IgnacioPardo/e36-obd/hardware/elm-backpack/viewer.html

E36 / HARDWARE · REV E

# Inline ECU adapter

48 mm narrow body · Hidden mounting · Rear USB

FIT CHECK REQUIRED

WebGL is unavailable. Open assembled.png or exploded.png in the exports folder.

Drag to orbit · Scroll to zoom · Double-click to reset

## Assembly

ClosedOpenExploded

Silver highlights · optional paint

## Separation

Printed base Boards and connectors ELM reference housing

Enclosure

162 × 48 × 30.4

Printed parts

6

Wall / floor

2.4 / 2.4*

USB opening

32 wide

Wire entry

16 × 12

*Floor is 1.4 mm beneath recessed mounting straps. The longer tail has a separate support-tie position.

The ELM housing and electronics are provisional packaging references. Verify the real boards, solder and wire heights, contact areas and tail hole before printing the full enclosure.

## Files

Print layout · 3MFFirst print · fit gauge STLEditable assembly · STEPMeasurement sources and design planPrinting and assembly instructions
