IgnacioPardo/e36-obd/hardware/elm-backpack/exports/black.png

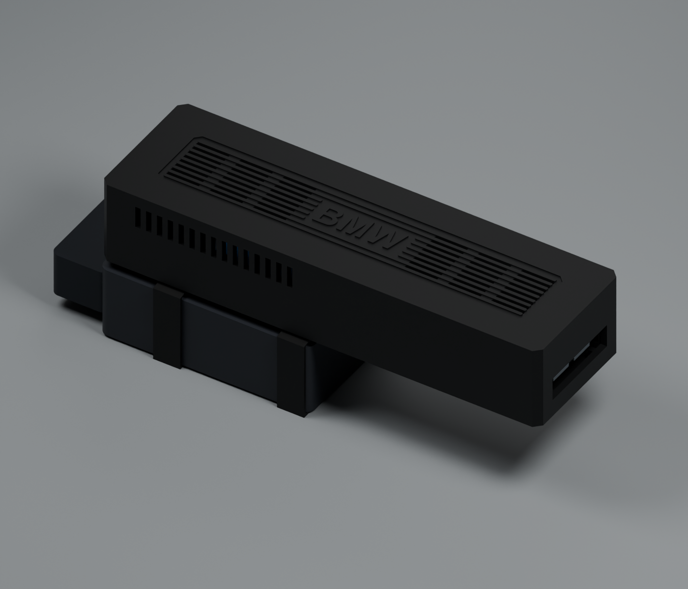
hardware/elm-backpack/exports/black.png
