IgnacioPardo/e36-obd/hardware/elm-backpack/exports/comparison.png

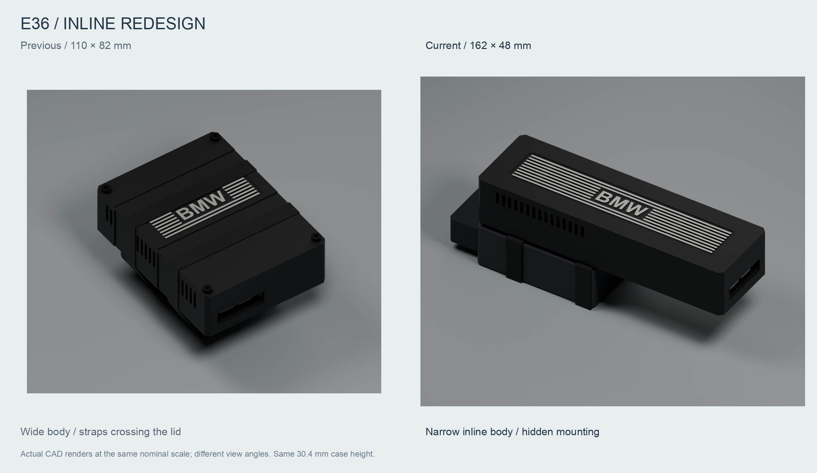
hardware/elm-backpack/exports/comparison.png
