IgnacioPardo/e36-obd/hardware/elm-backpack/exports/exploded-views/mounts-raw.png

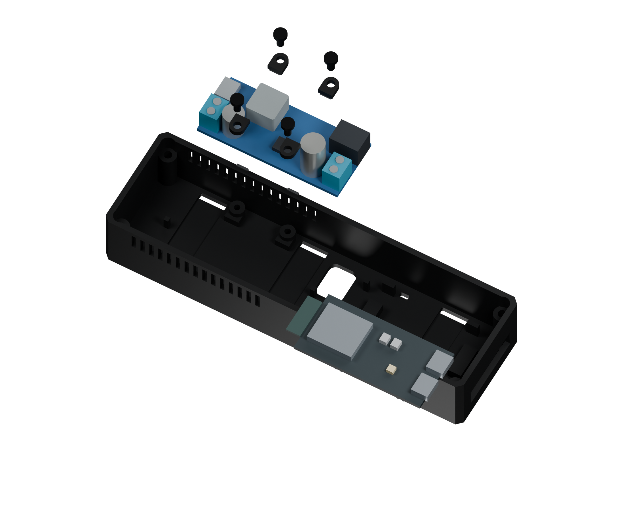
hardware/elm-backpack/exports/exploded-views/mounts-raw.png
