IgnacioPardo/e36-obd/hardware/elm-backpack/exports/exploded-views/mounts.png

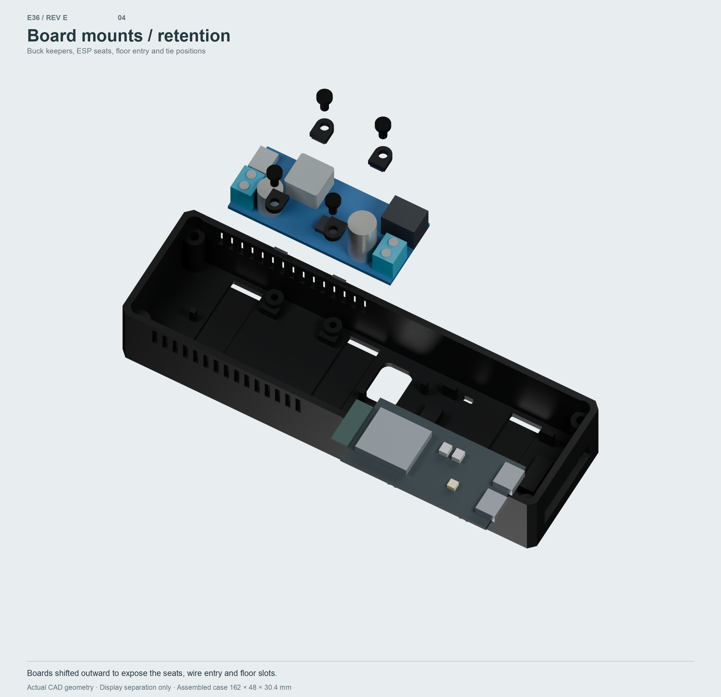
hardware/elm-backpack/exports/exploded-views/mounts.png
