IgnacioPardo/e36-obd/hardware/elm-backpack/exports/exploded-views/reverse-raw.png

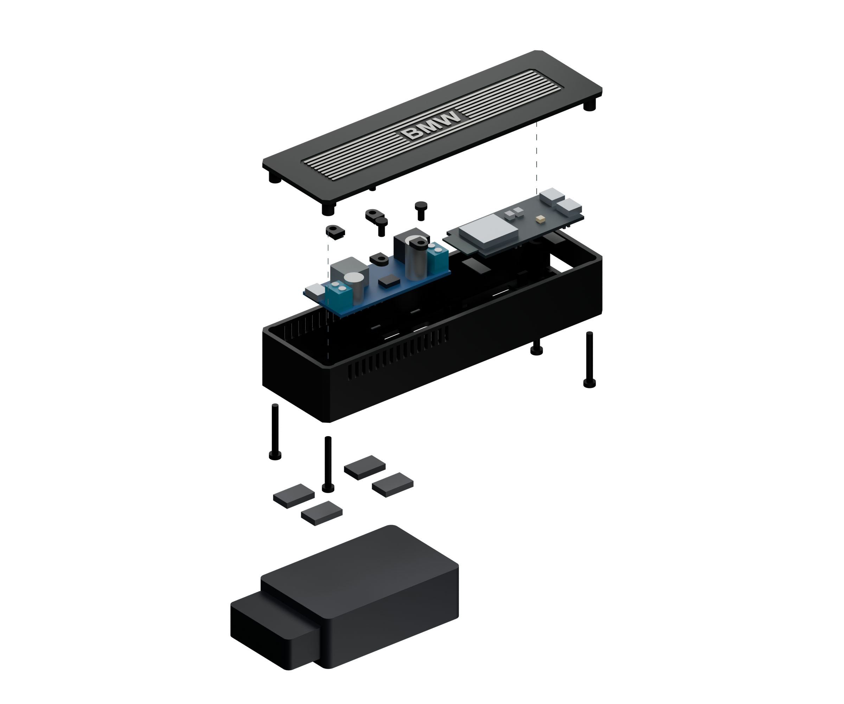
hardware/elm-backpack/exports/exploded-views/reverse-raw.png
