IgnacioPardo/e36-obd/hardware/elm-backpack/exports/exploded-views/reverse.png

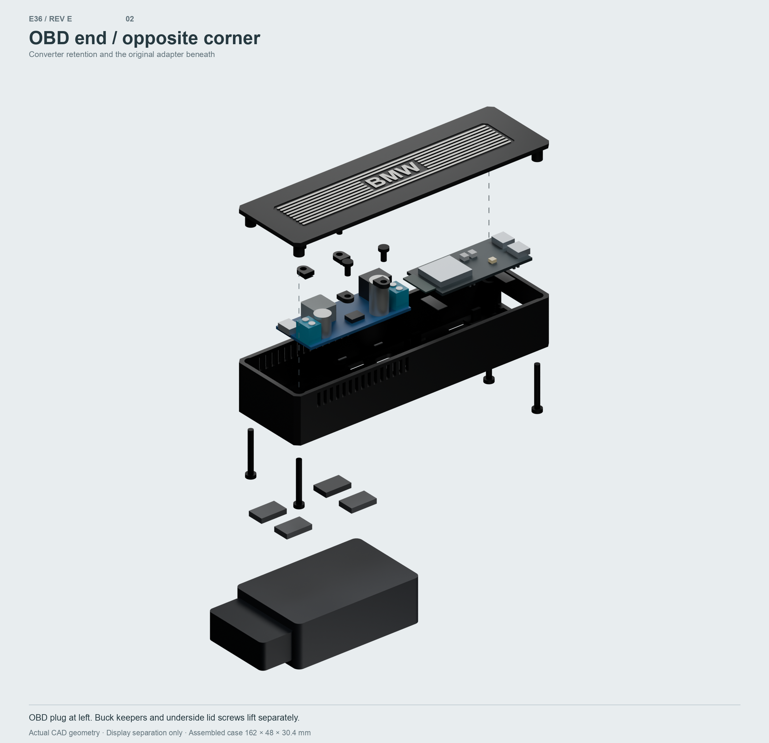
hardware/elm-backpack/exports/exploded-views/reverse.png
