IgnacioPardo/e36-obd/hardware/elm-backpack/exports/exploded-views/underside-raw.png

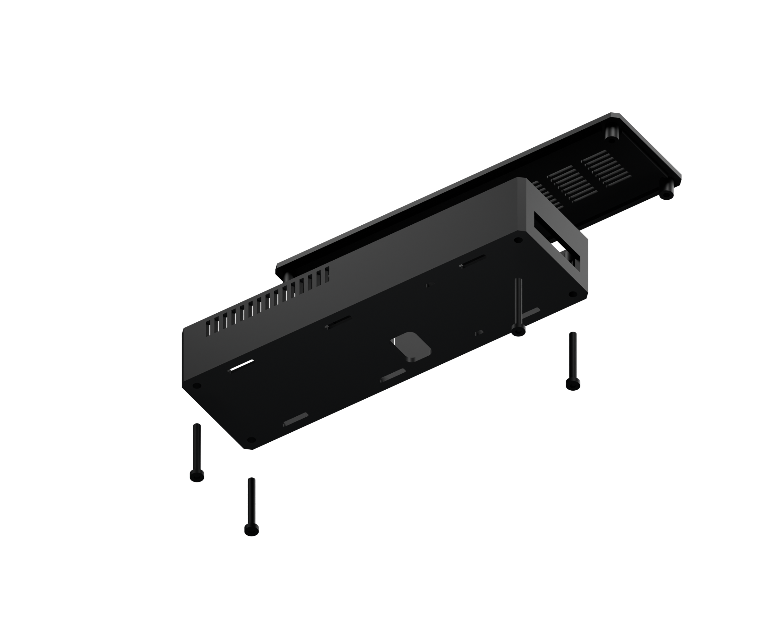
hardware/elm-backpack/exports/exploded-views/underside-raw.png
