IgnacioPardo/e36-obd/hardware/elm-backpack/exports/exploded-views/underside.png

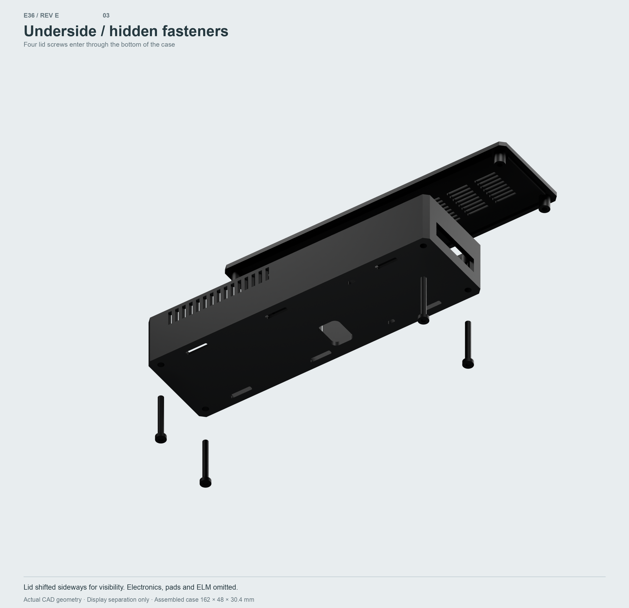
hardware/elm-backpack/exports/exploded-views/underside.png
