IgnacioPardo/e36-obd/hardware/elm-backpack/exports/exploded.png

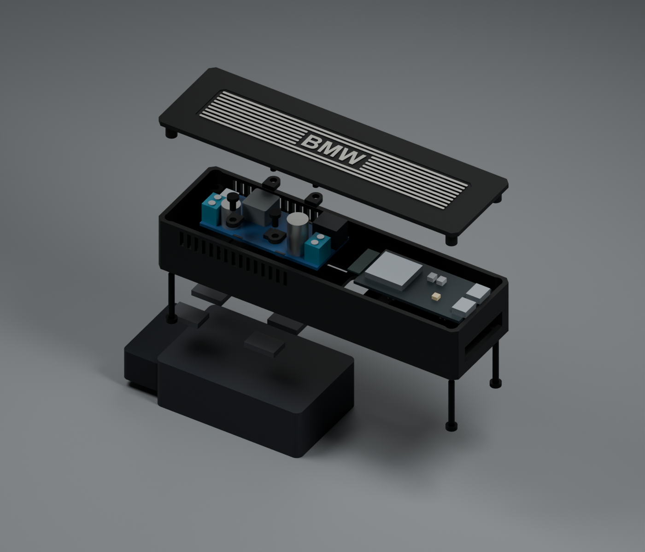
hardware/elm-backpack/exports/exploded.png
