IgnacioPardo/e36-obd/hardware/elm-backpack/exports/interior.png

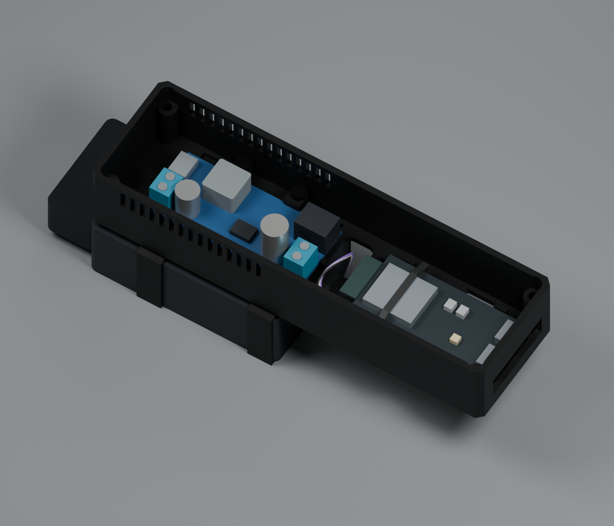
hardware/elm-backpack/exports/interior.png
