IgnacioPardo/e36-obd/hardware/elm-backpack/references/1oUab5/Screenshot 2026-09-07 at 21.01.18.png

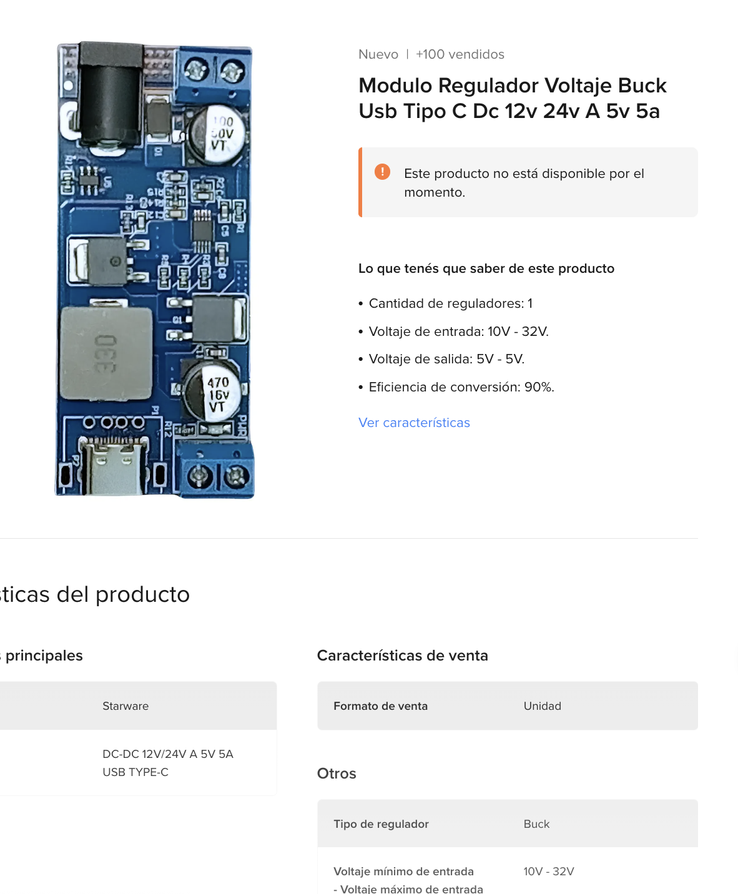
hardware/elm-backpack/references/1oUab5/Screenshot 2026-09-07 at 21.01.18.png
