IgnacioPardo/e36-obd/hardware/elm-backpack/references/bQd2Rp/WhatsApp Image 2026-09-07 at 21.03.03 (1).jpeg

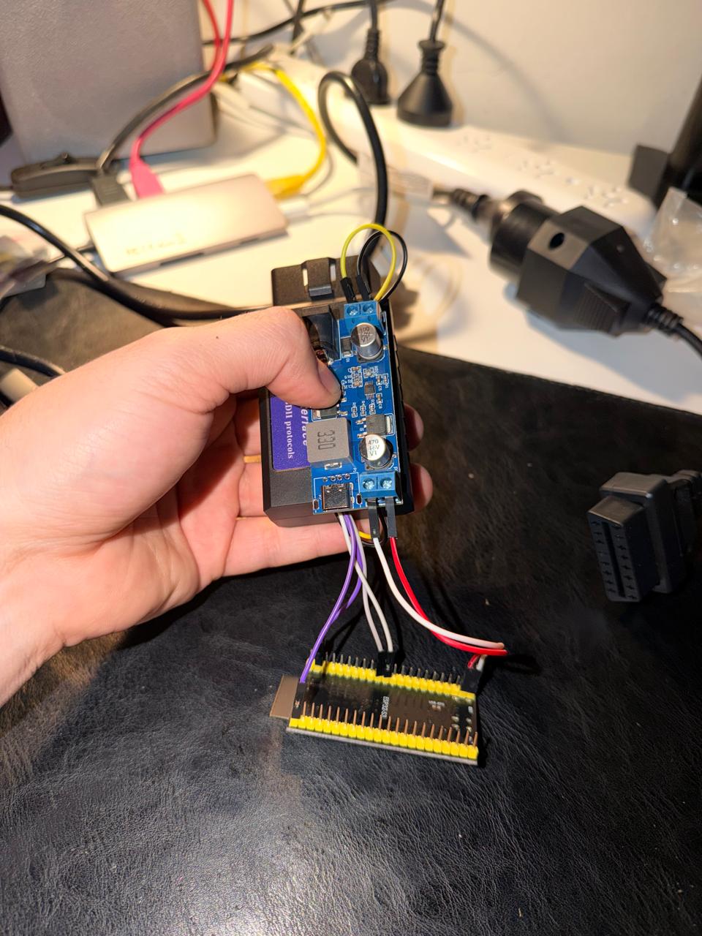
hardware/elm-backpack/references/bQd2Rp/WhatsApp Image 2026-09-07 at 21.03.03 (1).jpeg
