IgnacioPardo/e36-obd/hardware/elm-backpack/references/BzqjeP/WhatsApp Image 2026-09-07 at 21.03.03.jpeg

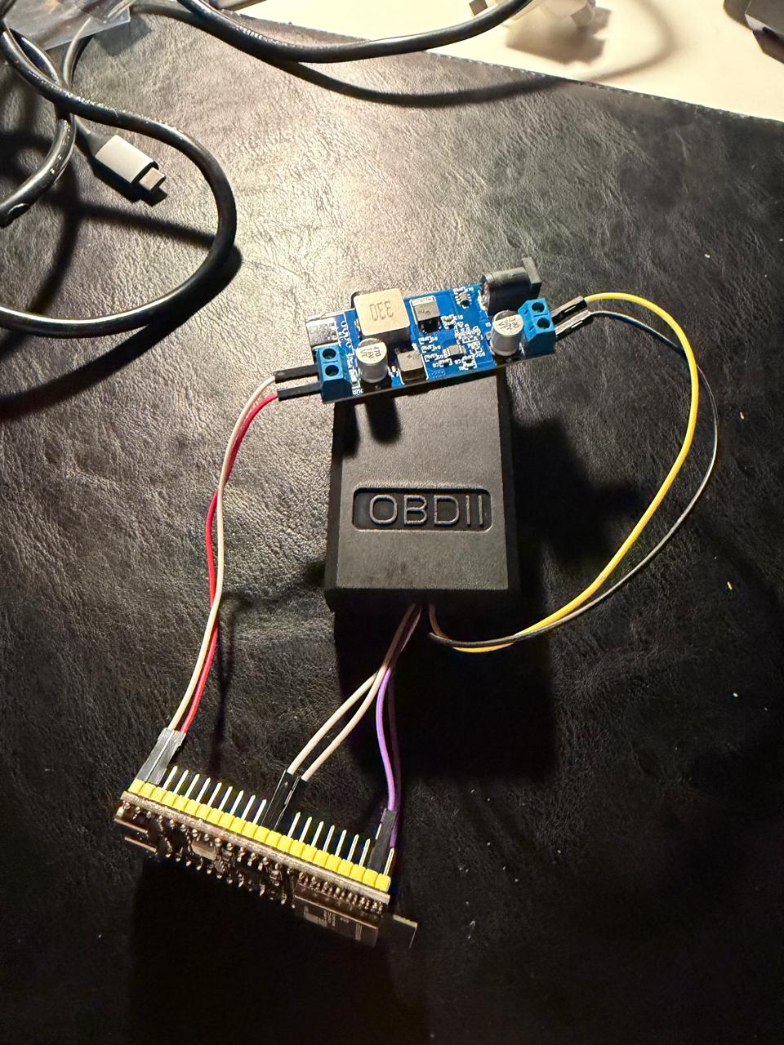
hardware/elm-backpack/references/BzqjeP/WhatsApp Image 2026-09-07 at 21.03.03.jpeg
