IgnacioPardo/e36-obd/hardware/elm-backpack/references/C2j69D/image.png

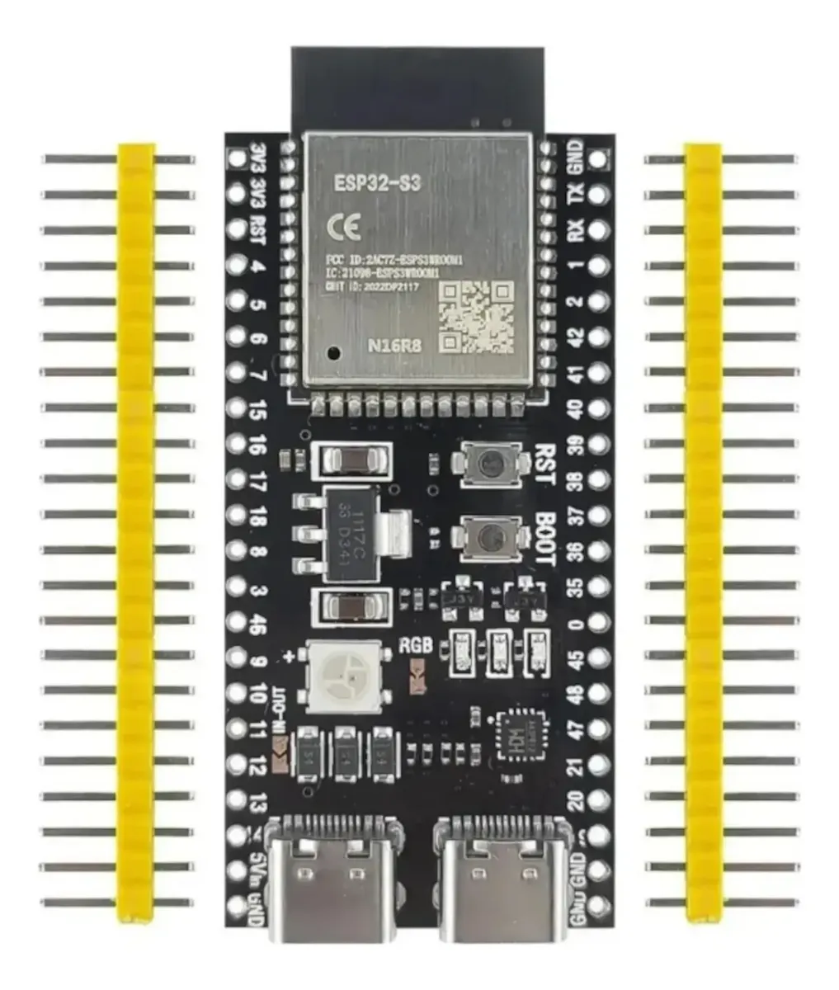
hardware/elm-backpack/references/C2j69D/image.png
