IgnacioPardo/e36-obd/hardware/elm-backpack/references/C7Ws7u/image.png

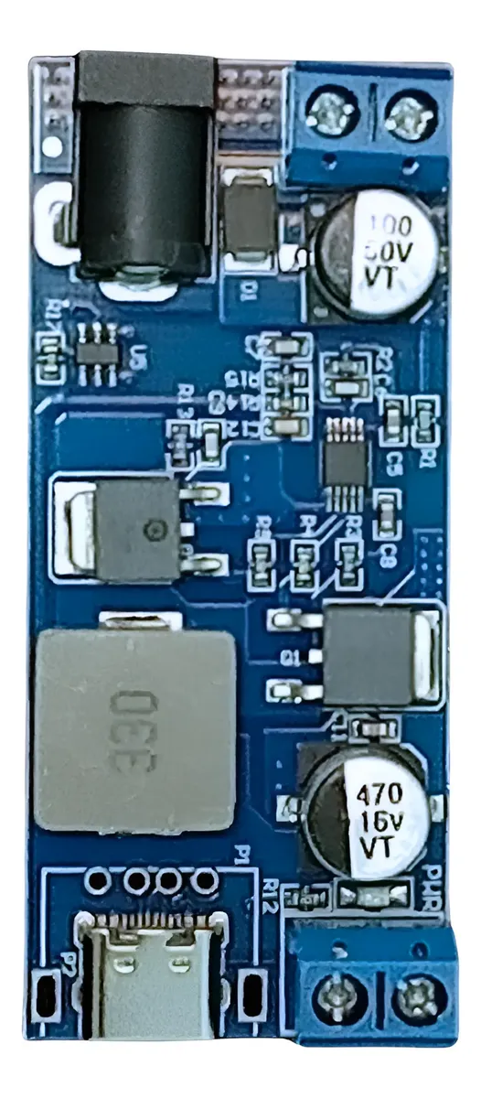
hardware/elm-backpack/references/C7Ws7u/image.png
