IgnacioPardo/e36-obd/hardware/elm-backpack/references/IZgJo3/WhatsApp Image 2026-09-07 at 21.03.03 (2).jpeg

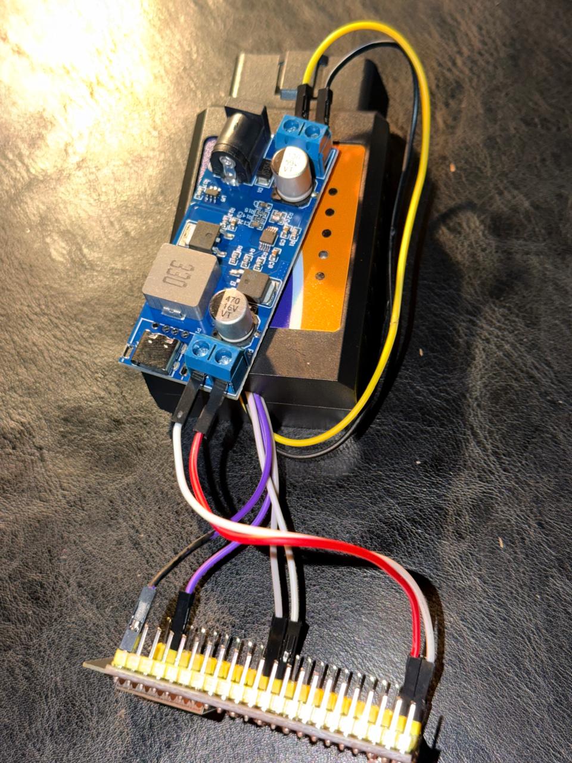
hardware/elm-backpack/references/IZgJo3/WhatsApp Image 2026-09-07 at 21.03.03 (2).jpeg
