IgnacioPardo/e36-obd/hardware/elm-backpack/references/JtD1lp/Screenshot 2026-09-07 at 21.01.42.png

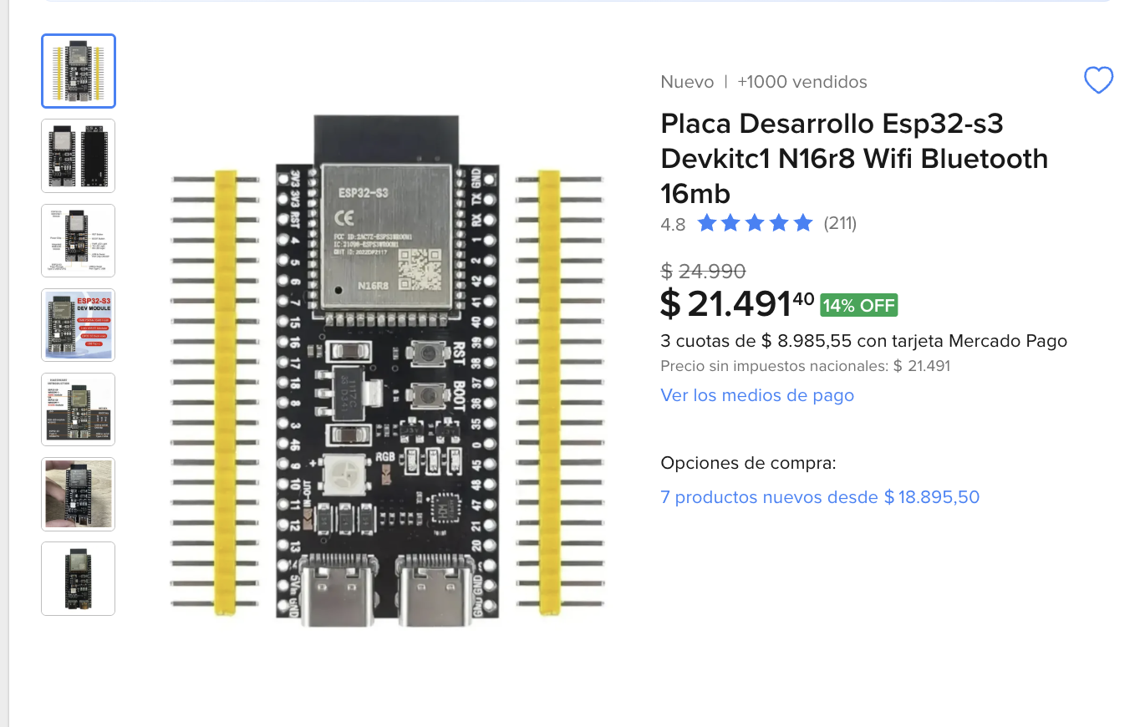
hardware/elm-backpack/references/JtD1lp/Screenshot 2026-09-07 at 21.01.42.png
