IgnacioPardo/e36-obd/hardware/elm-backpack/references/NnfwtA/Screenshot 2026-09-07 at 21.02.11.png

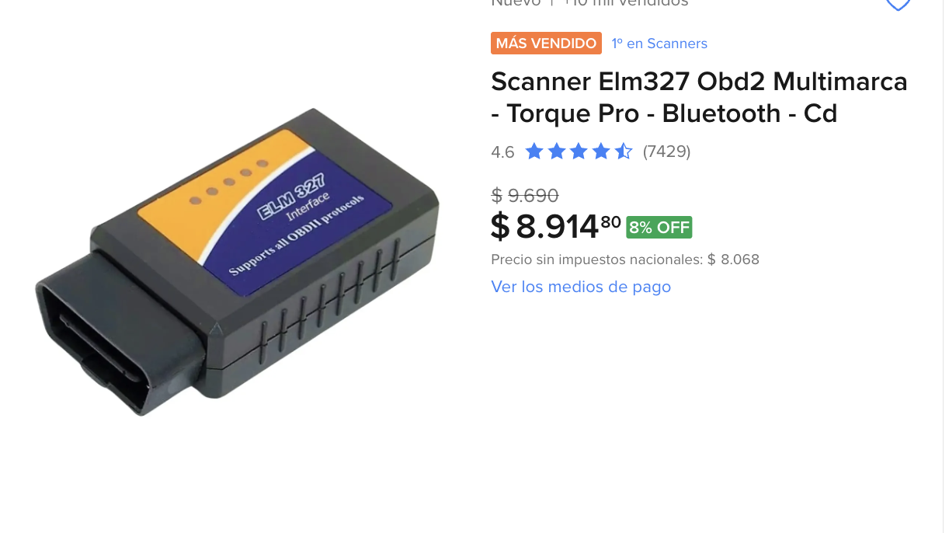
hardware/elm-backpack/references/NnfwtA/Screenshot 2026-09-07 at 21.02.11.png
