IgnacioPardo/e36-obd/hardware/onboard/case/render-board.png

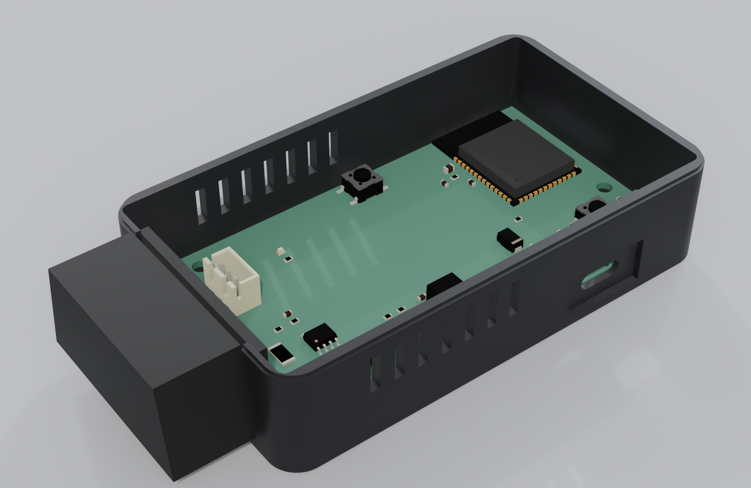
hardware/onboard/case/render-board.png
