IgnacioPardo/e36-obd/hardware/onboard/case/render-connector-end.png

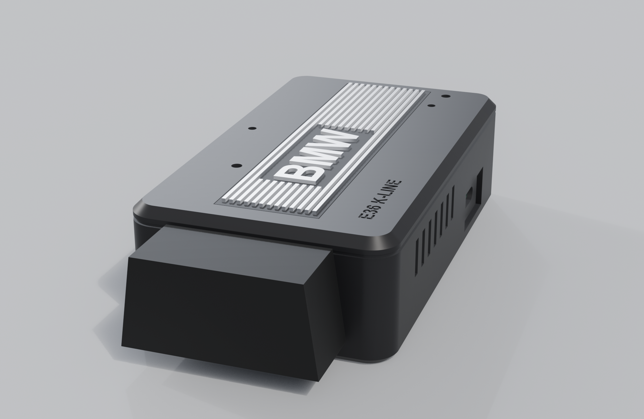
hardware/onboard/case/render-connector-end.png
