IgnacioPardo/e36-obd/hardware/onboard/case/render-rear.png

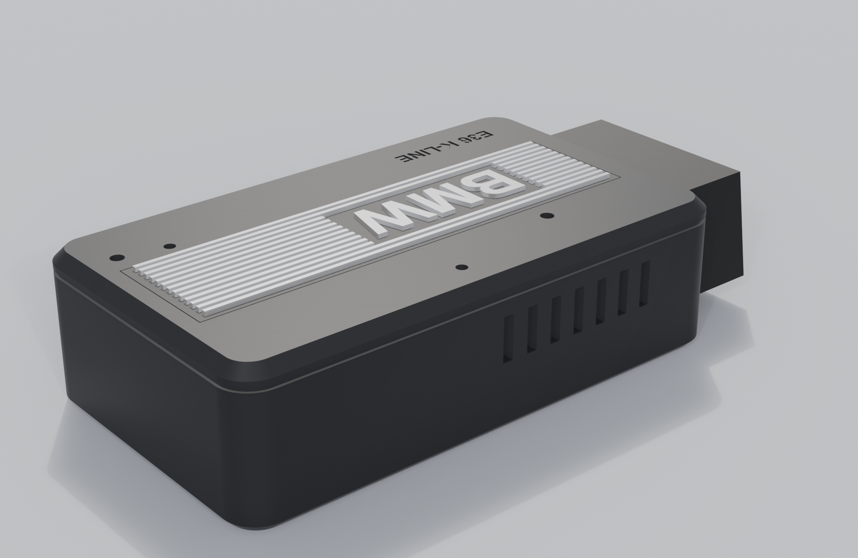
hardware/onboard/case/render-rear.png
