IgnacioPardo/e36-obd/hardware/onboard/fab/bottom.png

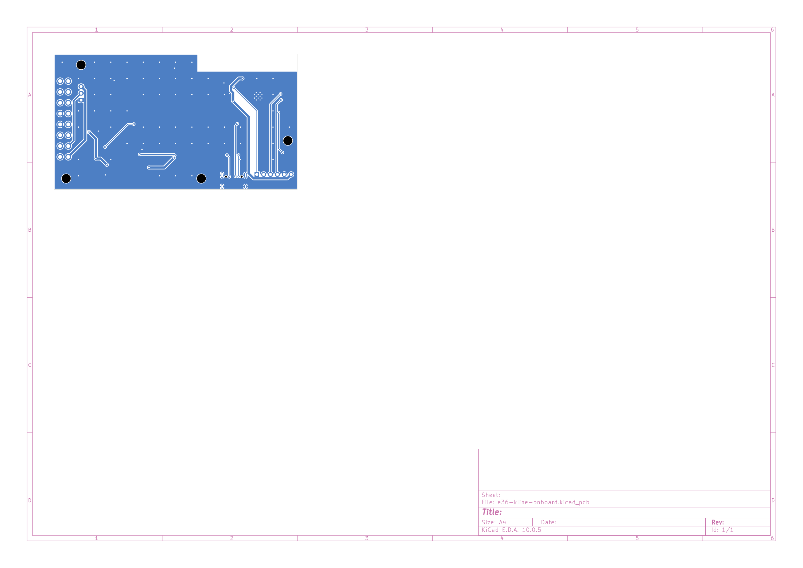
hardware/onboard/fab/bottom.png
