IgnacioPardo/e36-obd/hardware/onboard/fab/render-bottom.png

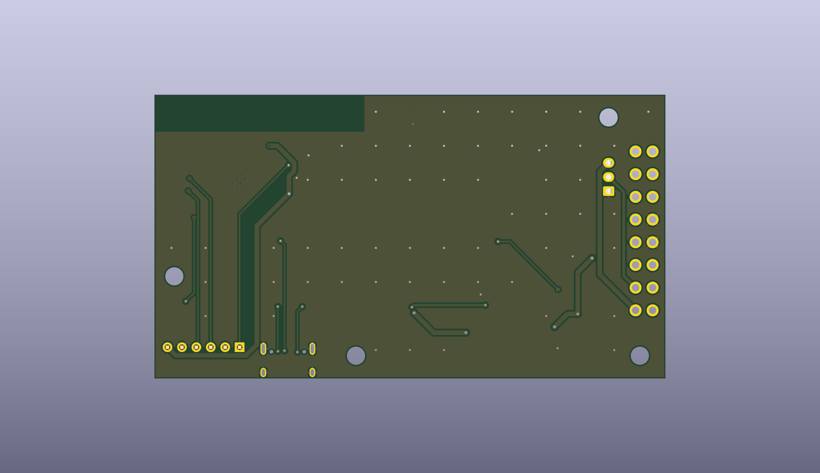
hardware/onboard/fab/render-bottom.png
