IgnacioPardo/e36-obd/hardware/onboard/fab/silk.png

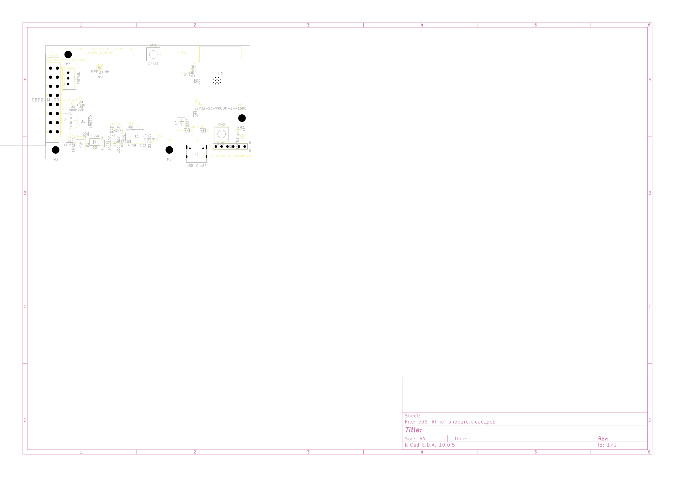
hardware/onboard/fab/silk.png
