IgnacioPardo/e36-obd/hardware/onboard/fab/top-copper.png

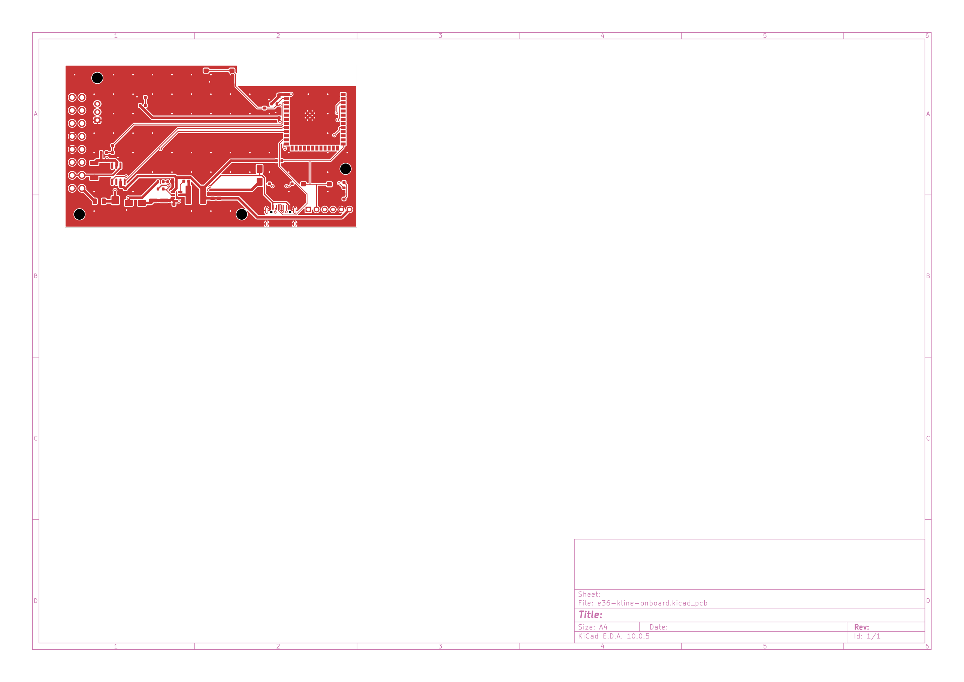
hardware/onboard/fab/top-copper.png
