IgnacioPardo/e36-obd/ios/Design/Camera/detail-portrait.jpg

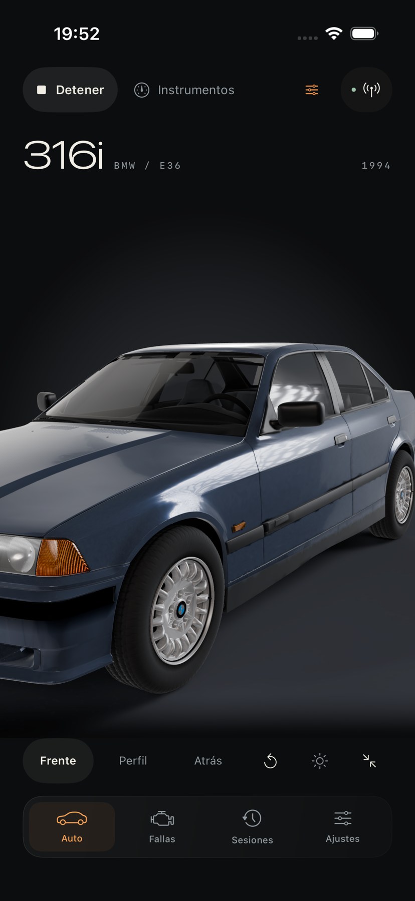
ios/Design/Camera/detail-portrait.jpg
