IgnacioPardo/e36-obd/ios/Design/Camera/orbit-landscape.jpg

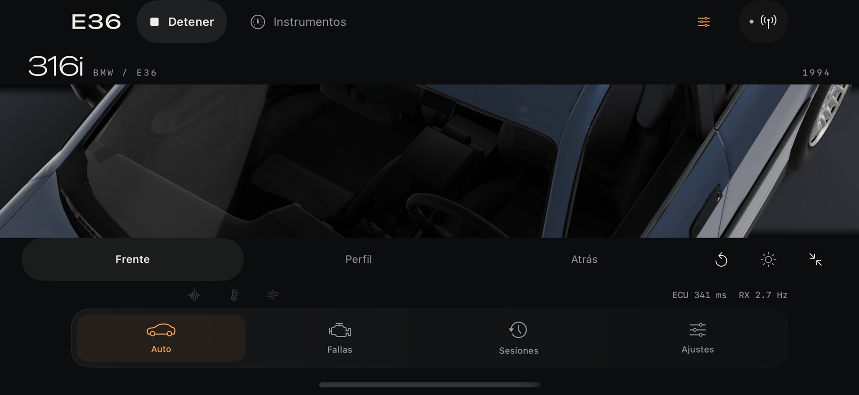
ios/Design/Camera/orbit-landscape.jpg
