IgnacioPardo/e36-obd/ios/Design/Camera/reset-landscape.jpg

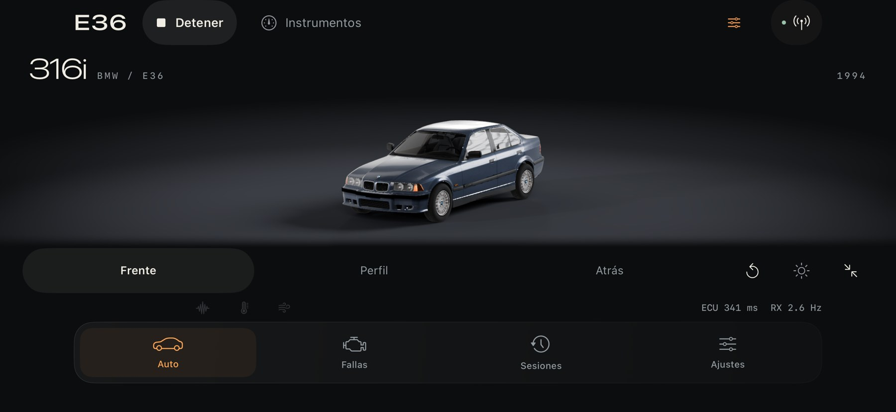
ios/Design/Camera/reset-landscape.jpg
