IgnacioPardo/e36-obd/ios/Design/Companion/41-complication-rectangular.png

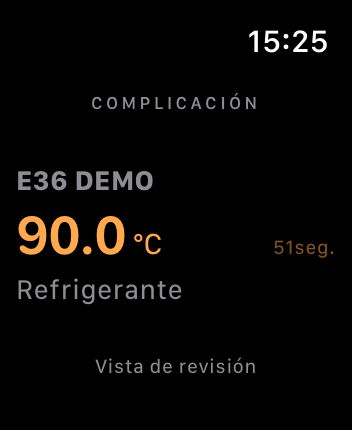
ios/Design/Companion/41-complication-rectangular.png
