IgnacioPardo/e36-obd/ios/Design/Companion/41-coolant-normal.png

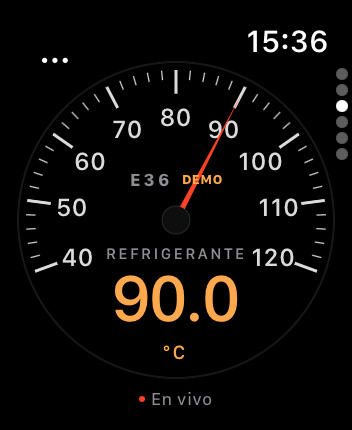
ios/Design/Companion/41-coolant-normal.png
