IgnacioPardo/e36-obd/ios/Design/Companion/41-intake-normal.png

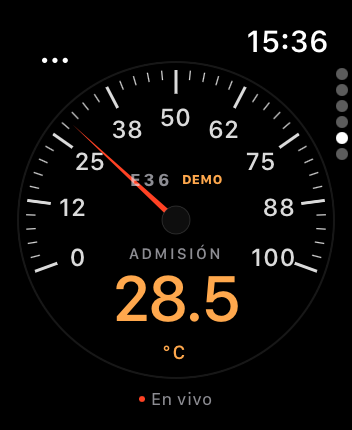
ios/Design/Companion/41-intake-normal.png
