IgnacioPardo/e36-obd/ios/Design/Companion/41-load-normal.png

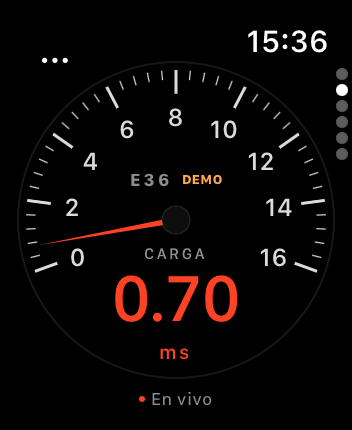
ios/Design/Companion/41-load-normal.png
