IgnacioPardo/e36-obd/ios/Design/Companion/41-overview-normal.png

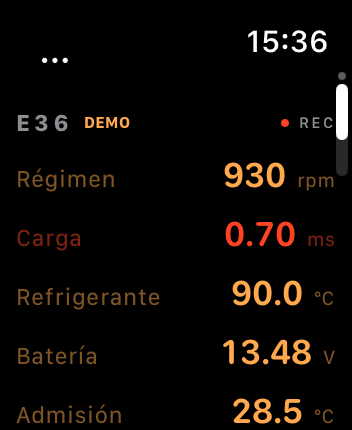
ios/Design/Companion/41-overview-normal.png
