IgnacioPardo/e36-obd/ios/Design/Companion/41-rpm-normal.png

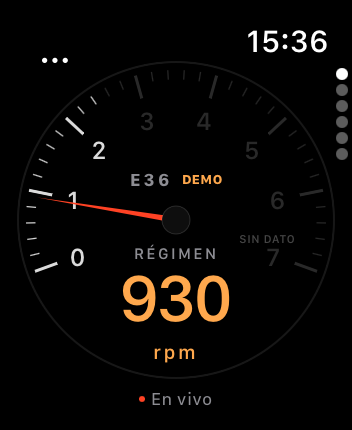
ios/Design/Companion/41-rpm-normal.png
