IgnacioPardo/e36-obd/ios/Design/Companion/45-complication-circular.png

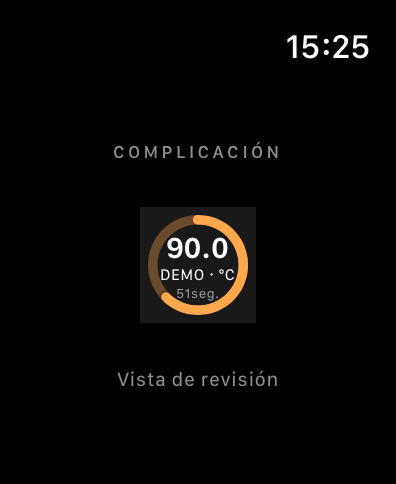
ios/Design/Companion/45-complication-circular.png
