IgnacioPardo/e36-obd/ios/Design/Companion/45-coolant-heat.png

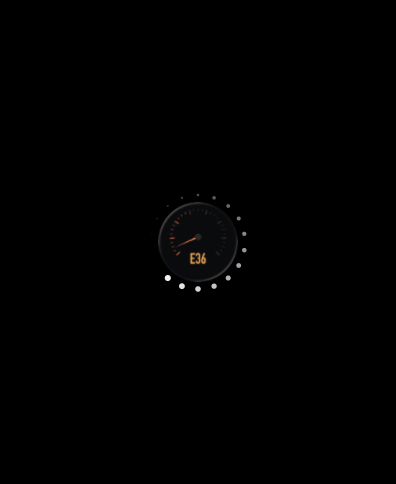
ios/Design/Companion/45-coolant-heat.png
