IgnacioPardo/e36-obd/ios/Design/Companion/45-intake-stale.png

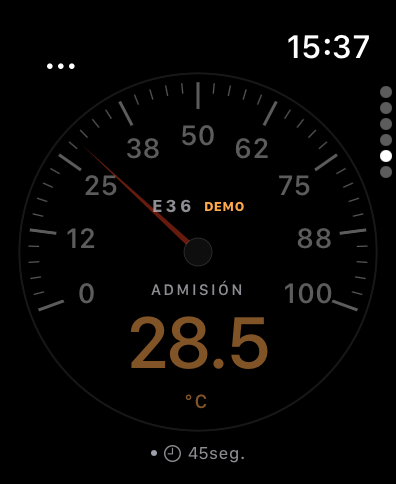
ios/Design/Companion/45-intake-stale.png
