IgnacioPardo/e36-obd/ios/Design/Companion/45-rpm-off.png

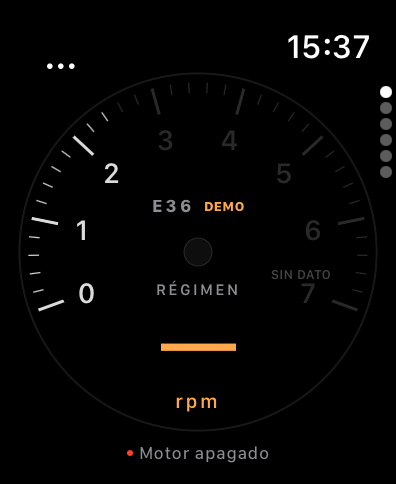
ios/Design/Companion/45-rpm-off.png
