IgnacioPardo/e36-obd/ios/Design/Companion/45-rpm-saturated.png

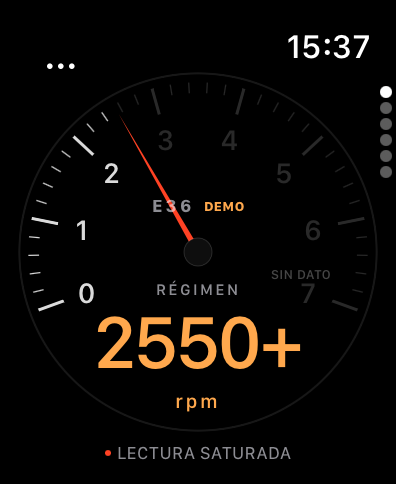
ios/Design/Companion/45-rpm-saturated.png
