IgnacioPardo/e36-obd/ios/Design/Companion/activity-full.png

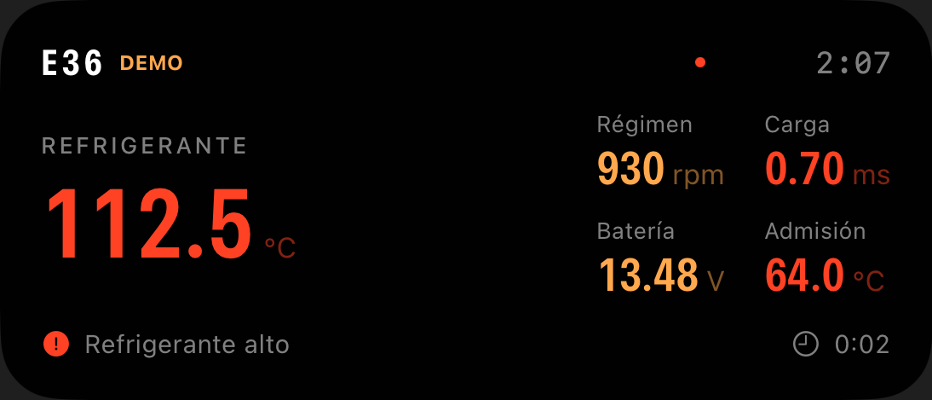
ios/Design/Companion/activity-full.png
