IgnacioPardo/e36-obd/ios/Design/Companion/activity-off.png

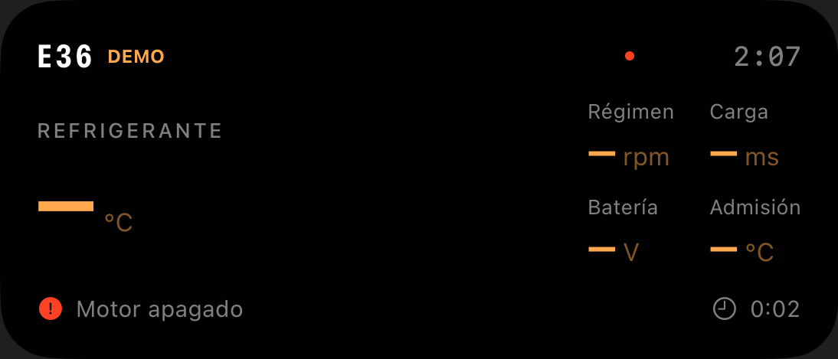
ios/Design/Companion/activity-off.png
