IgnacioPardo/e36-obd/ios/Design/Companion/activity-small.png

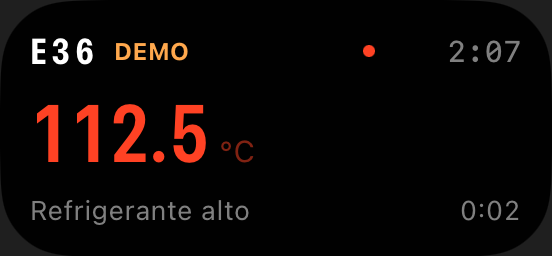
ios/Design/Companion/activity-small.png
