IgnacioPardo/e36-obd/ios/Design/Companion/island-compact.png

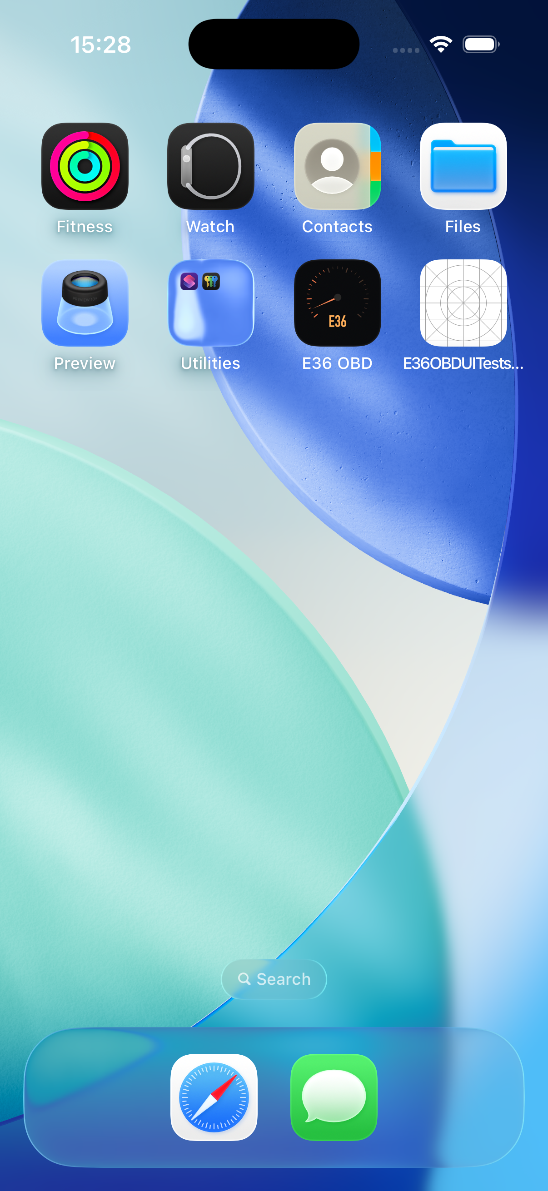
ios/Design/Companion/island-compact.png
