IgnacioPardo/e36-obd/ios/Design/Companion/island-expanded.png

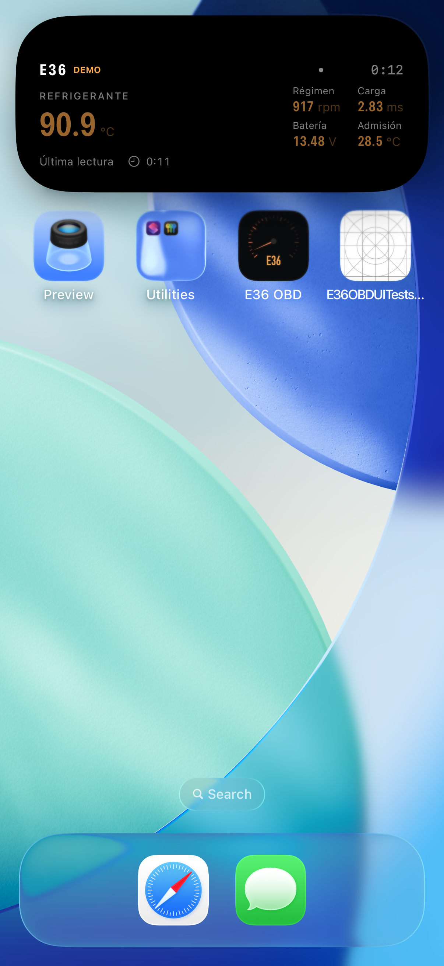
ios/Design/Companion/island-expanded.png
