IgnacioPardo/e36-obd/ios/Design/Companion/lock-screen.png

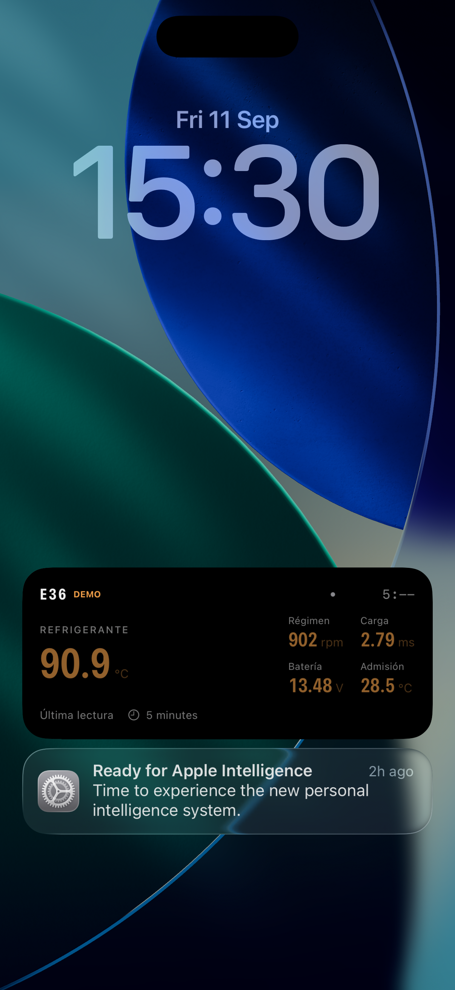
ios/Design/Companion/lock-screen.png
