IgnacioPardo/e36-obd/ios/Design/Companion/watch-preview.jpg

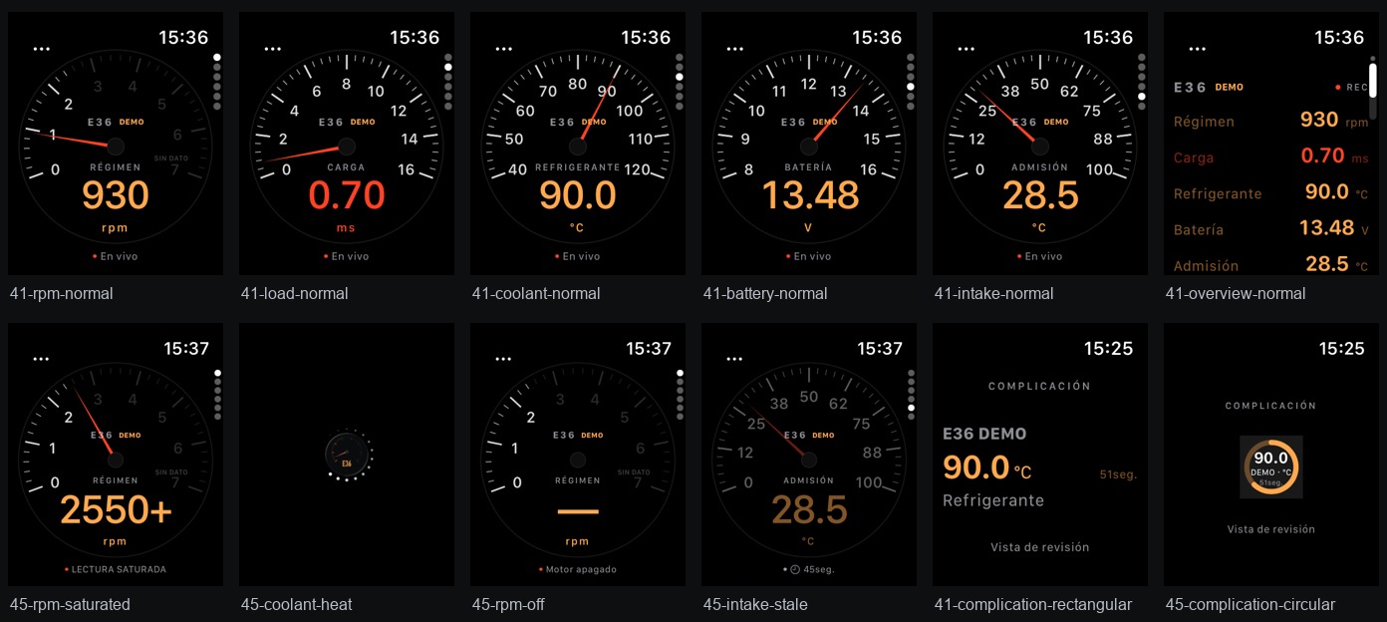
ios/Design/Companion/watch-preview.jpg
