IgnacioPardo/e36-obd/ios/Design/connection-landscape.jpg

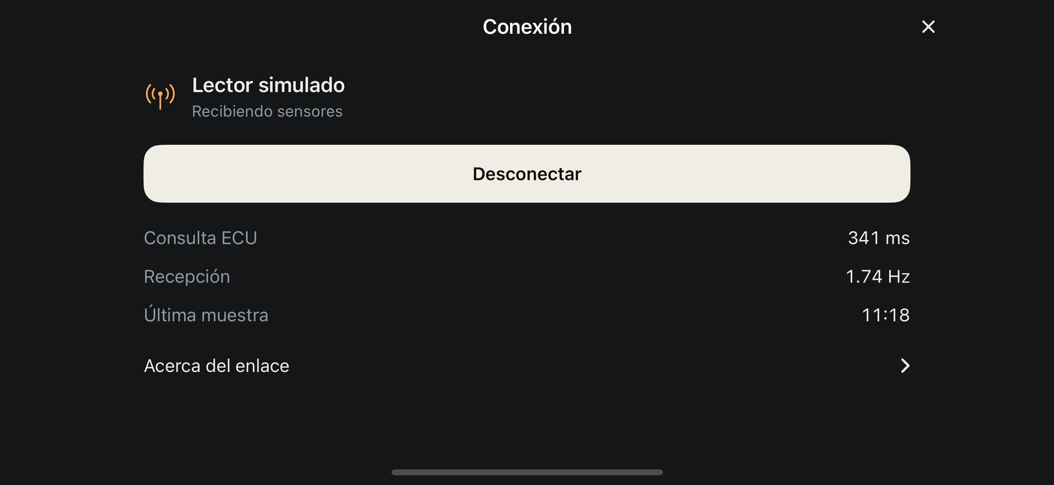
ios/Design/connection-landscape.jpg
