IgnacioPardo/e36-obd/ios/Design/connection-portrait.jpg

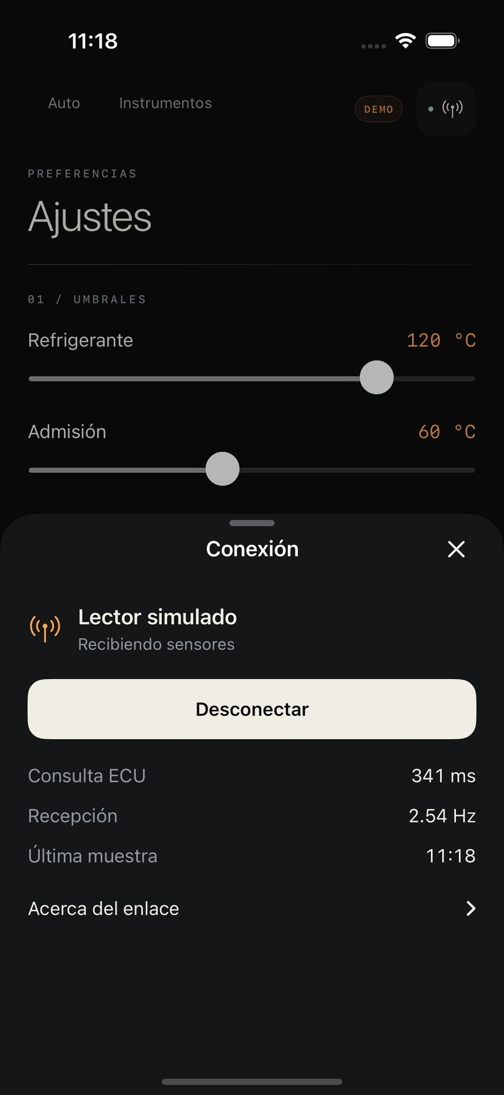
ios/Design/connection-portrait.jpg
