IgnacioPardo/e36-obd/ios/Design/exterior-landscape.jpg

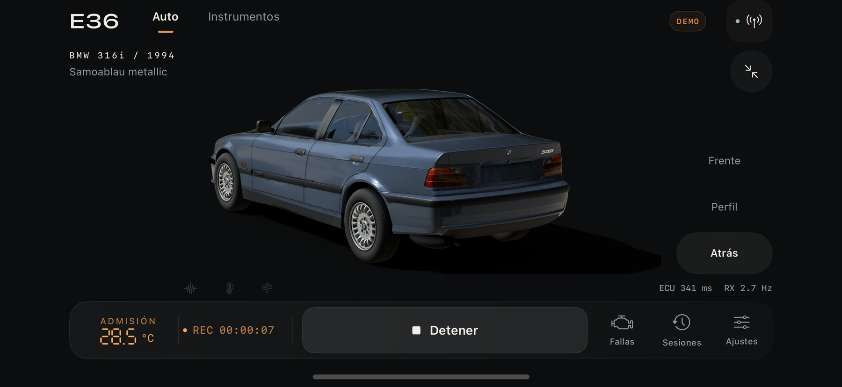
ios/Design/exterior-landscape.jpg
