IgnacioPardo/e36-obd/ios/Design/exterior-portrait.jpg

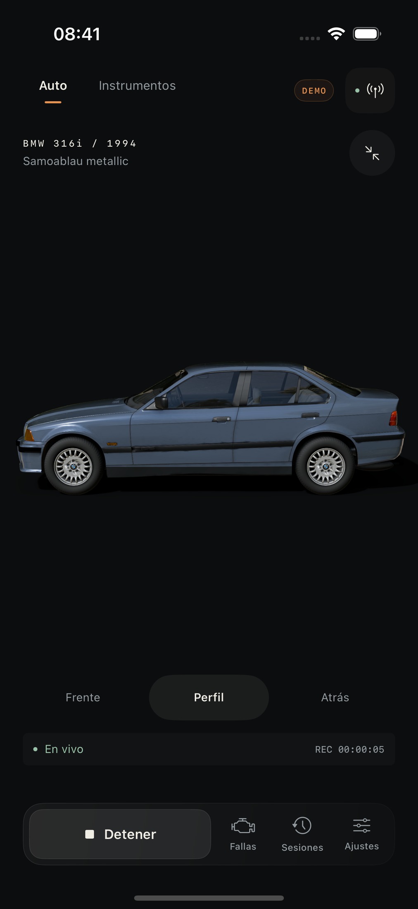
ios/Design/exterior-portrait.jpg
