IgnacioPardo/e36-obd/ios/Design/faults-portrait.jpg

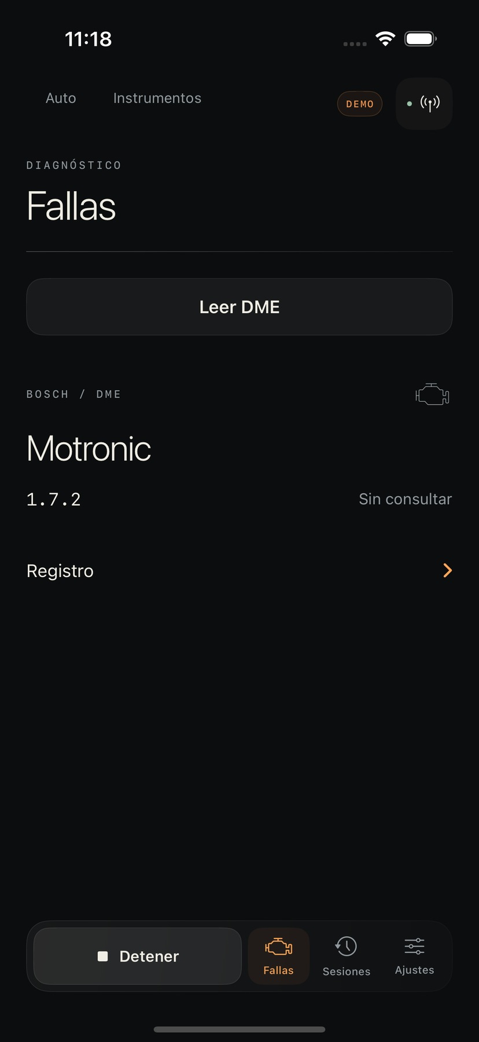
ios/Design/faults-portrait.jpg
