IgnacioPardo/e36-obd/ios/Design/headlamp-closeup.jpg

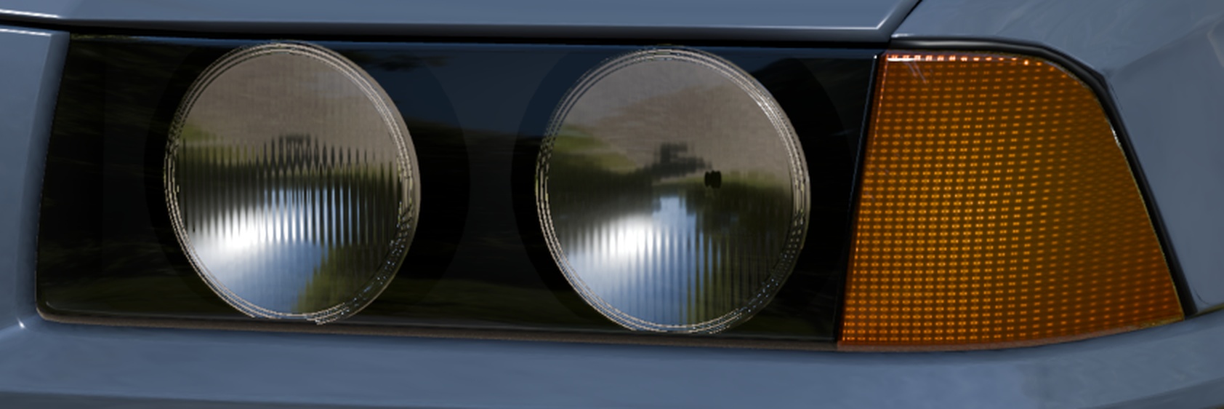
ios/Design/headlamp-closeup.jpg
