IgnacioPardo/e36-obd/ios/Design/headlamp-comparison.jpg

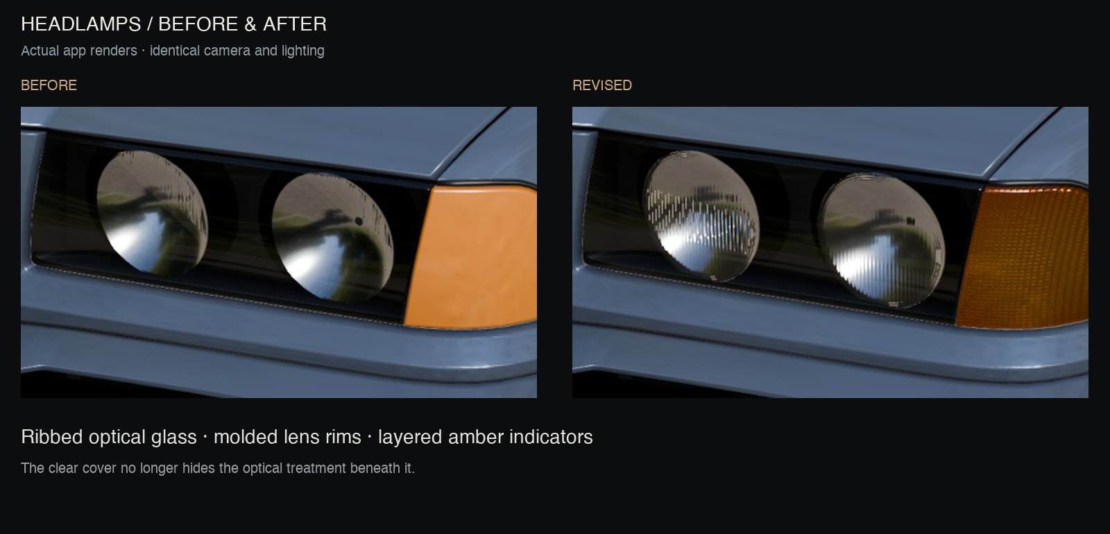
ios/Design/headlamp-comparison.jpg
