IgnacioPardo/e36-obd/ios/Design/lighting-comparison.jpg

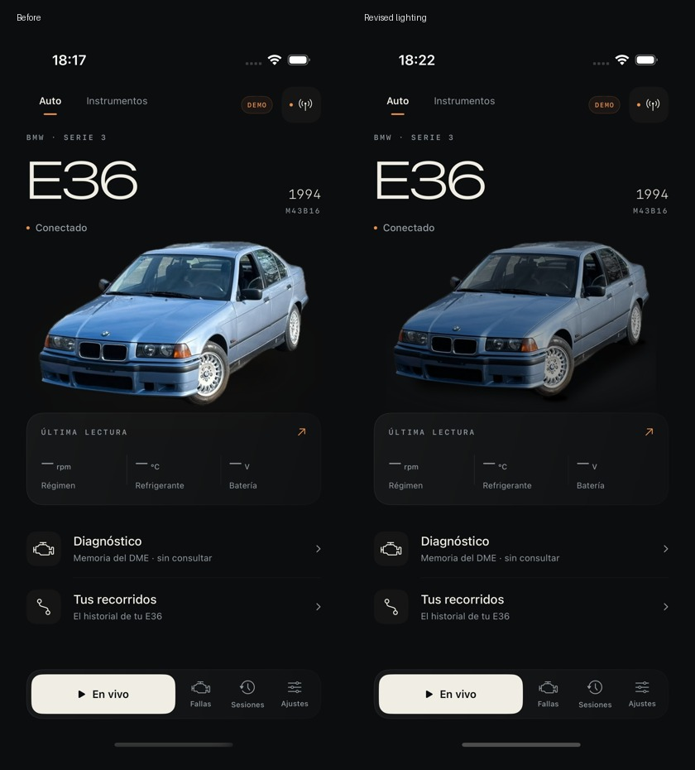
ios/Design/lighting-comparison.jpg
