IgnacioPardo/e36-obd/ios/Design/navigation-comparison.jpg

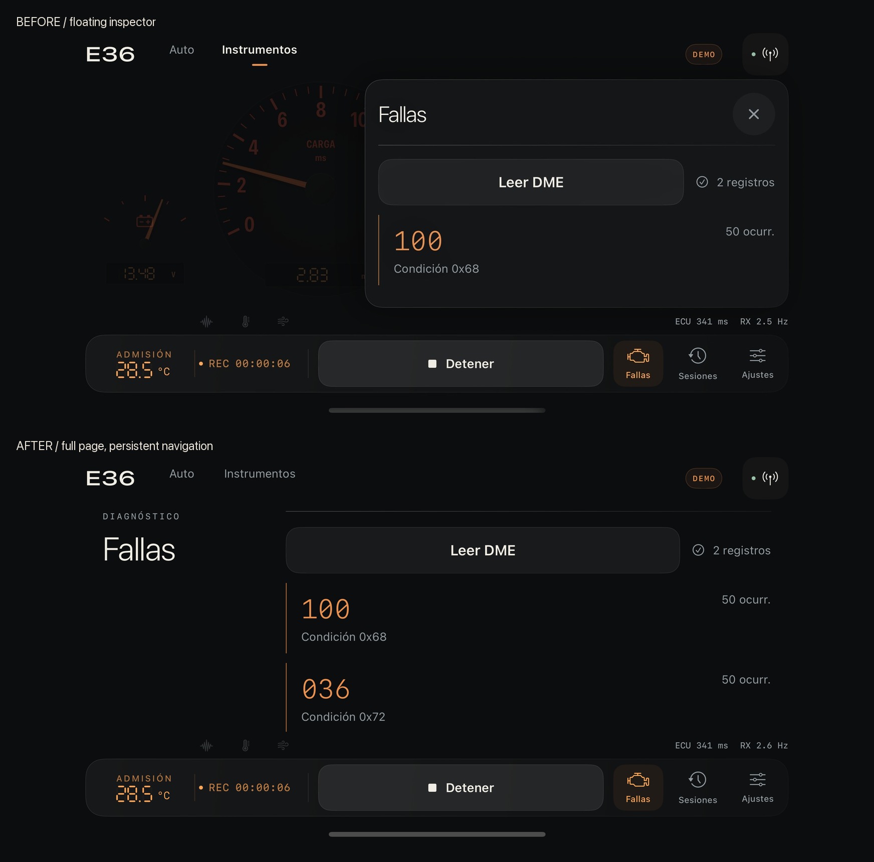
ios/Design/navigation-comparison.jpg
