IgnacioPardo/e36-obd/ios/Design/navigation-pages.jpg

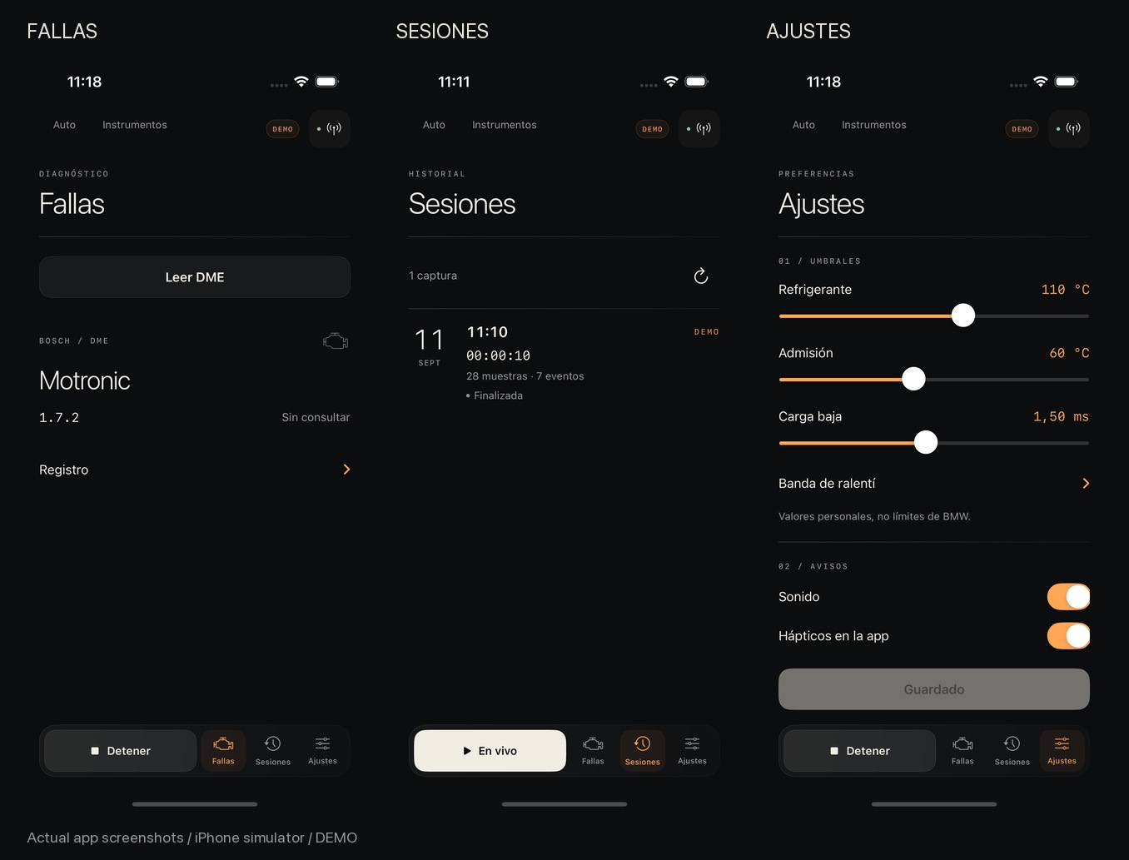
ios/Design/navigation-pages.jpg
