IgnacioPardo/e36-obd/ios/Design/Navigation/accessibility-landscape.jpg

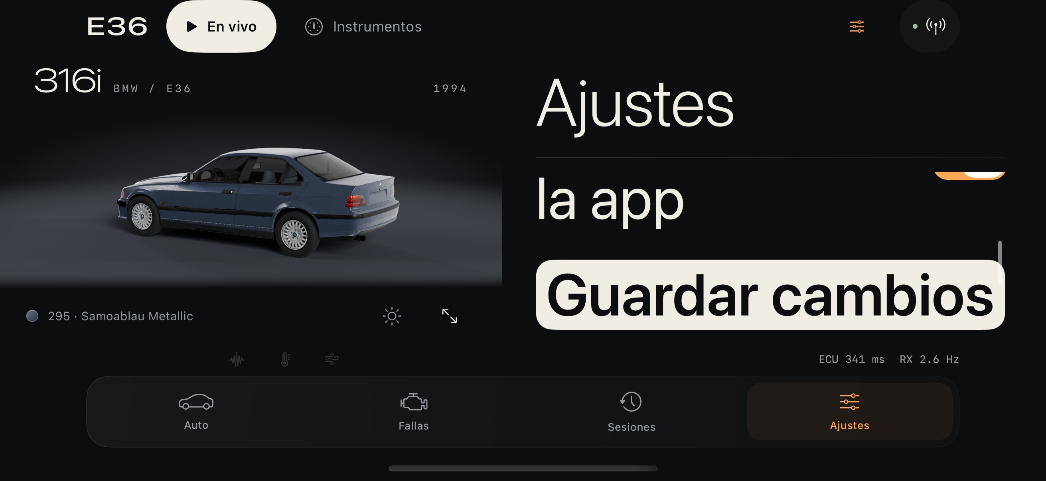
ios/Design/Navigation/accessibility-landscape.jpg
