IgnacioPardo/e36-obd/ios/Design/Navigation/ajustes-landscape.jpg

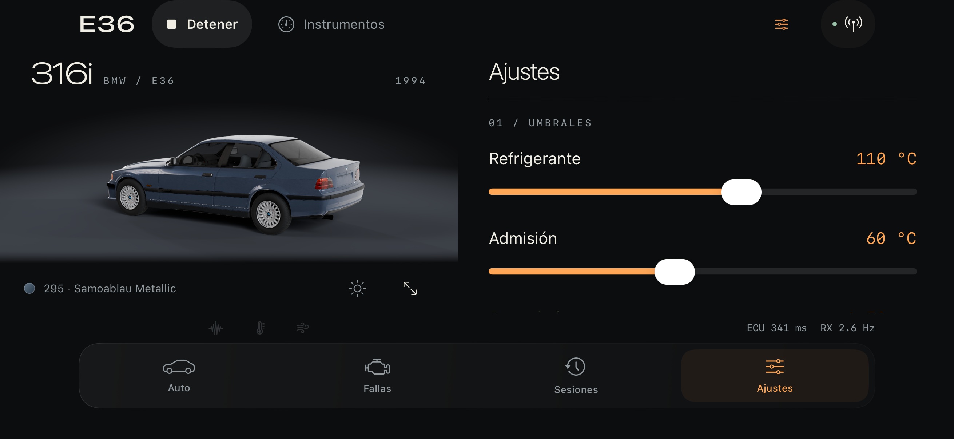
ios/Design/Navigation/ajustes-landscape.jpg
