IgnacioPardo/e36-obd/ios/Design/Navigation/ajustes-portrait.jpg

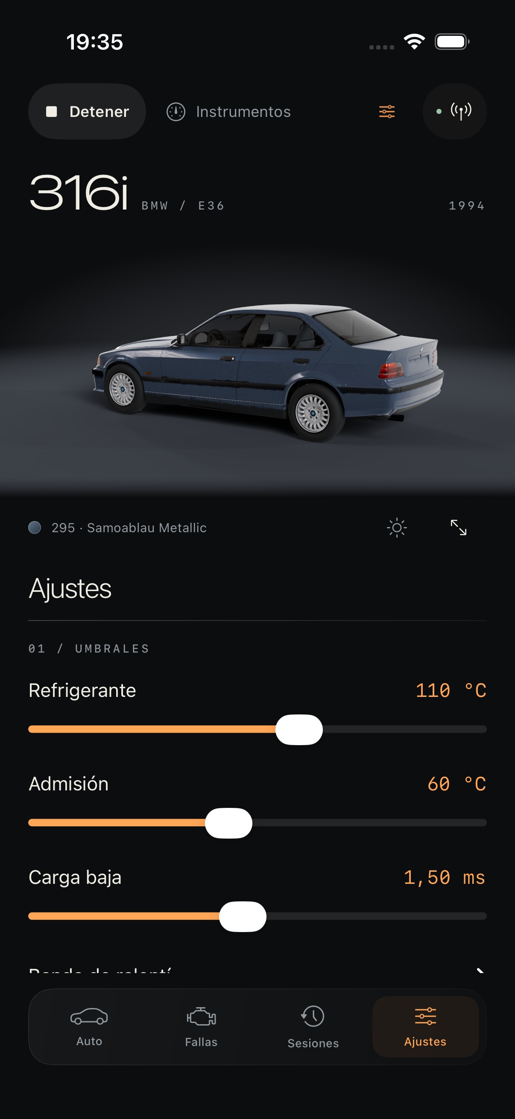
ios/Design/Navigation/ajustes-portrait.jpg
