IgnacioPardo/e36-obd/ios/Design/Navigation/auto-landscape.jpg

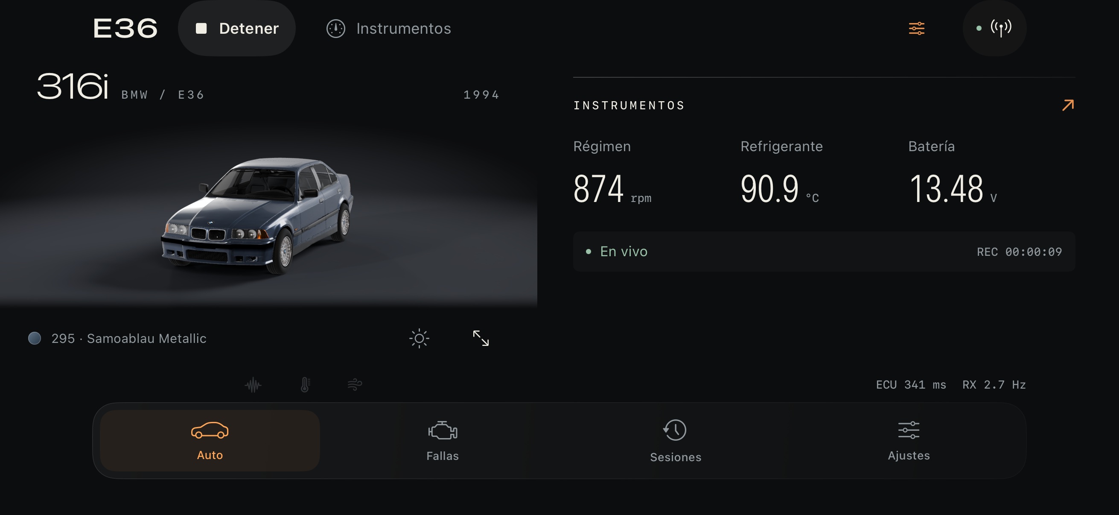
ios/Design/Navigation/auto-landscape.jpg
