IgnacioPardo/e36-obd/ios/Design/Navigation/fallas-landscape.jpg

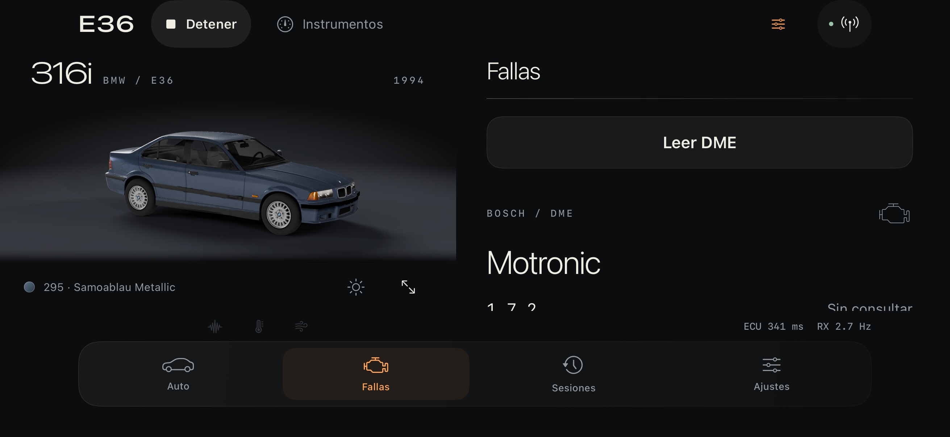
ios/Design/Navigation/fallas-landscape.jpg
