IgnacioPardo/e36-obd/ios/Design/Navigation/fallas-portrait.jpg

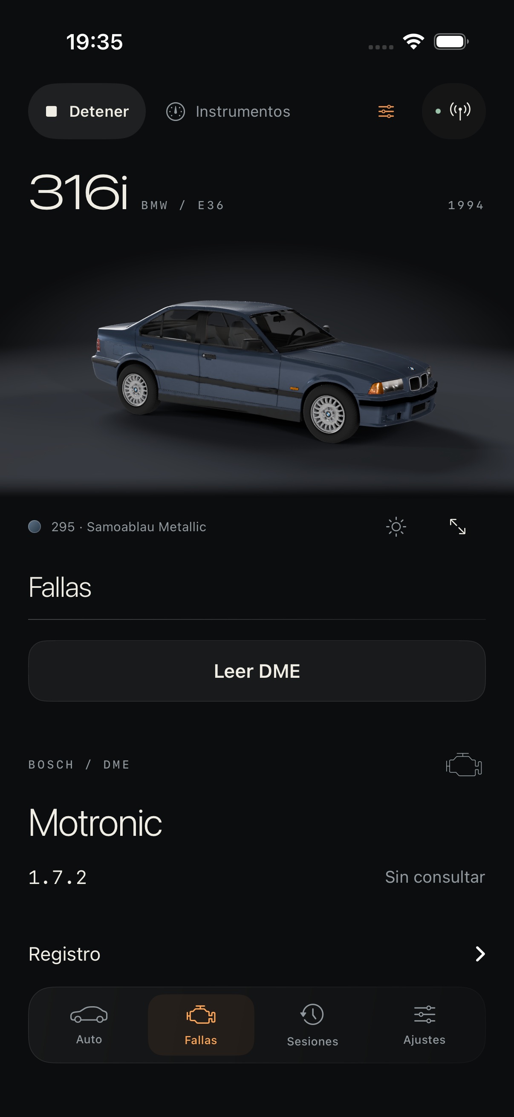
ios/Design/Navigation/fallas-portrait.jpg
