IgnacioPardo/e36-obd/ios/Design/Navigation/landscape-review.jpg

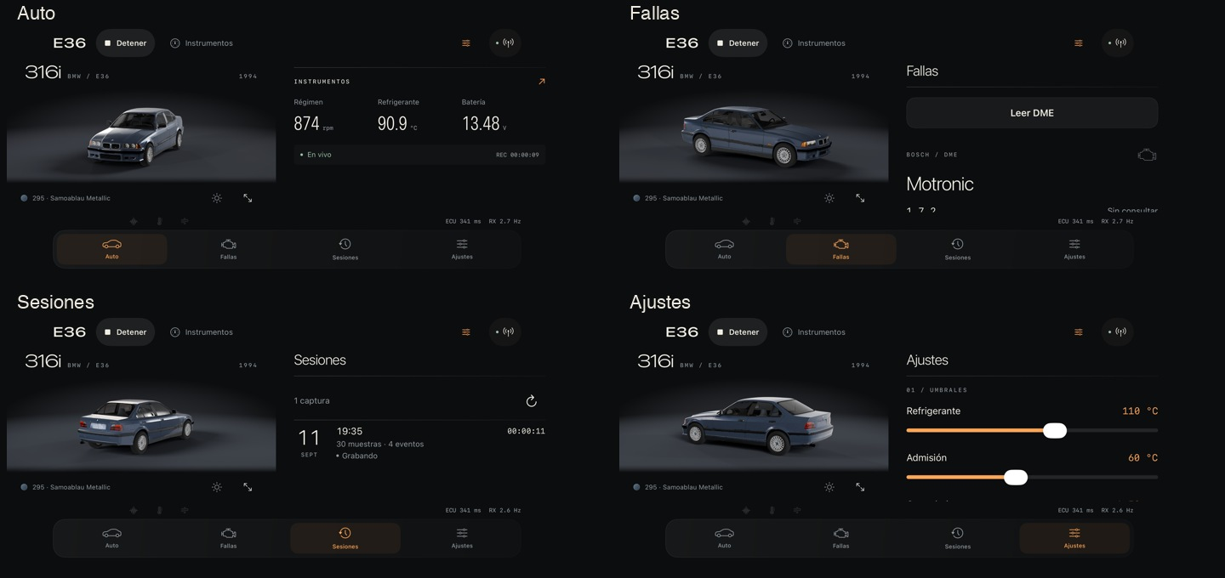
ios/Design/Navigation/landscape-review.jpg
