IgnacioPardo/e36-obd/ios/Design/Navigation/sesiones-landscape.jpg

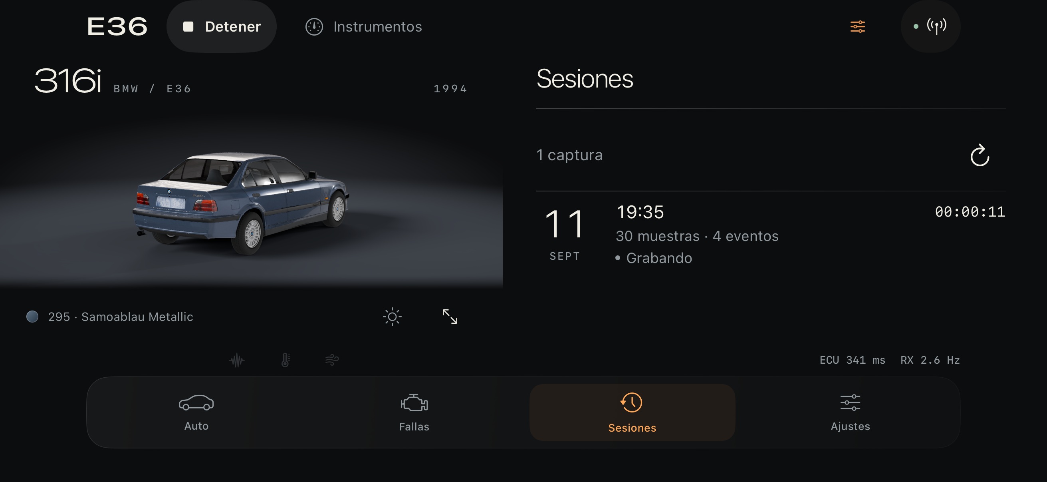
ios/Design/Navigation/sesiones-landscape.jpg
