IgnacioPardo/e36-obd/ios/Design/Navigation/sesiones-portrait.jpg

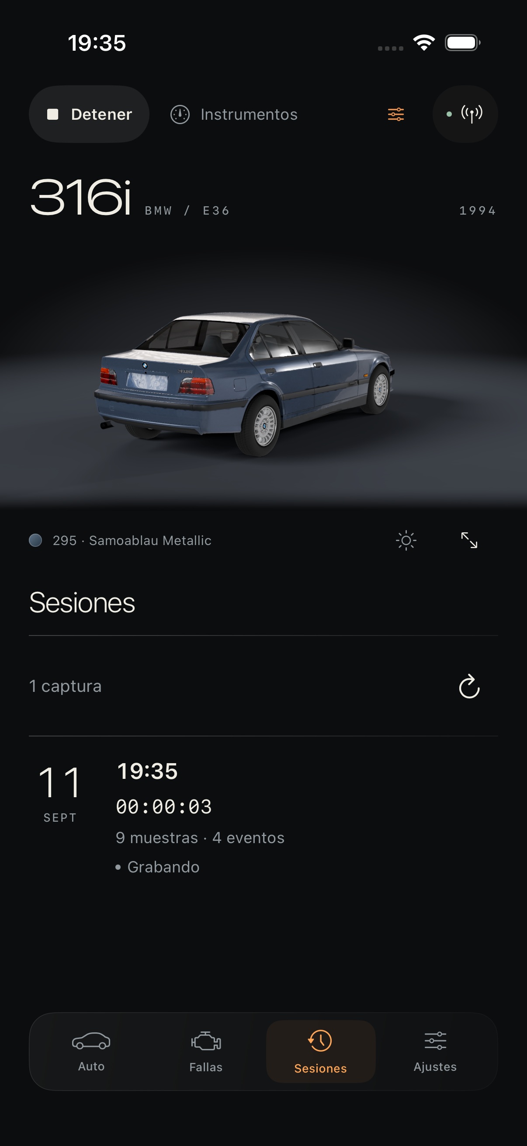
ios/Design/Navigation/sesiones-portrait.jpg
