IgnacioPardo/e36-obd/ios/Design/overview-landscape.jpg

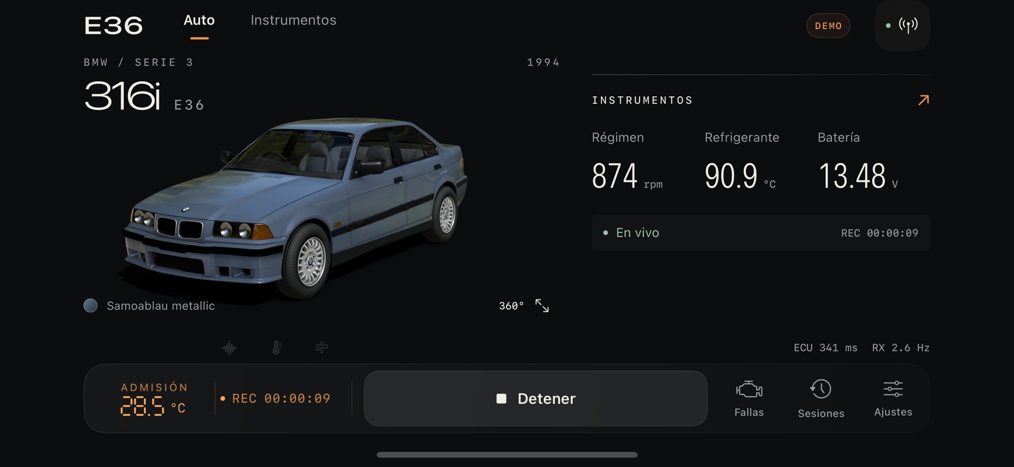
ios/Design/overview-landscape.jpg
