IgnacioPardo/e36-obd/ios/Design/overview-portrait.jpg

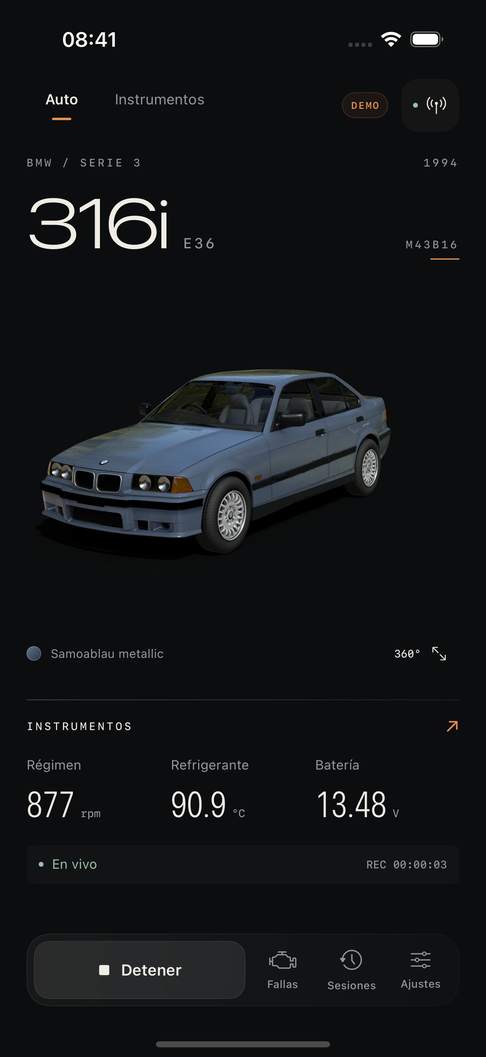
ios/Design/overview-portrait.jpg
