IgnacioPardo/e36-obd/ios/Design/paint-lighting-comparison.jpg

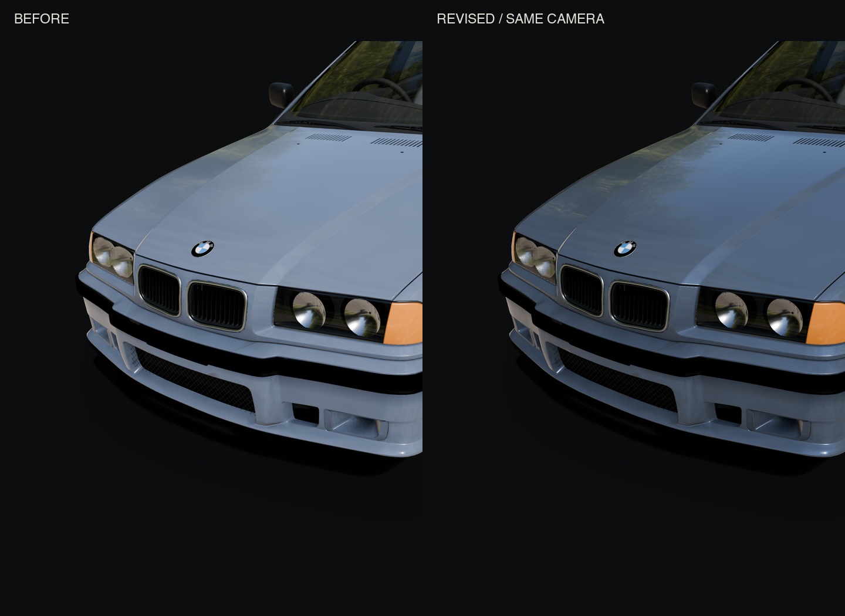
ios/Design/paint-lighting-comparison.jpg
