IgnacioPardo/e36-obd/ios/Design/preview.jpg

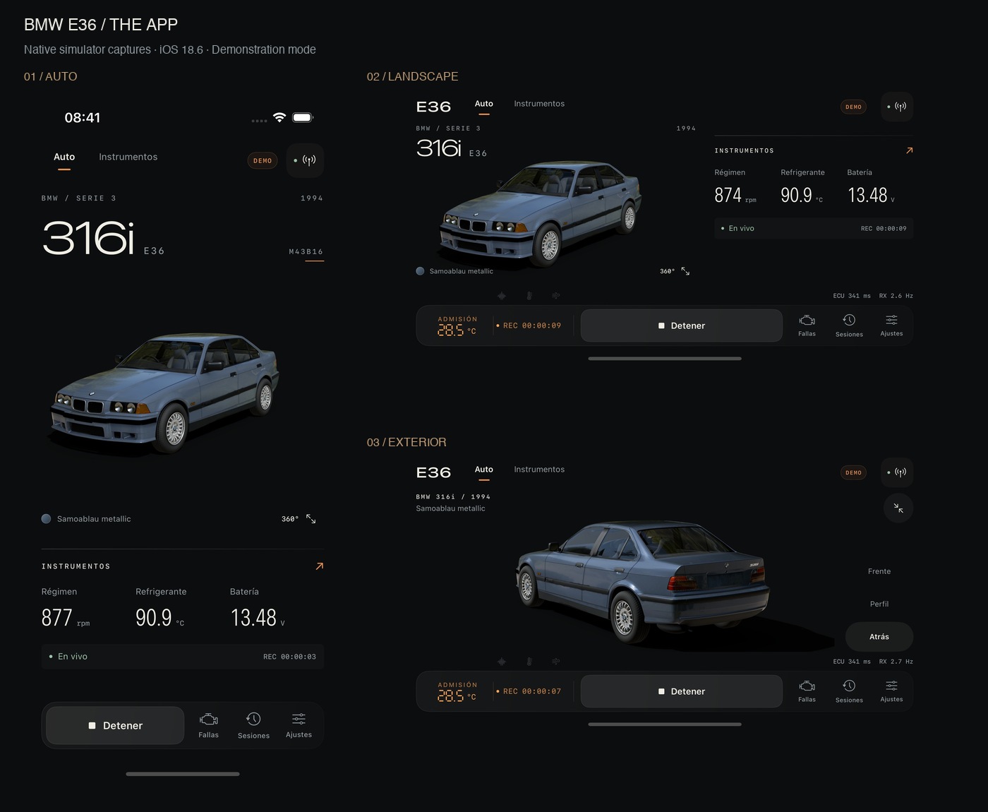
ios/Design/preview.jpg
