IgnacioPardo/e36-obd/ios/Design/sessions-landscape.jpg

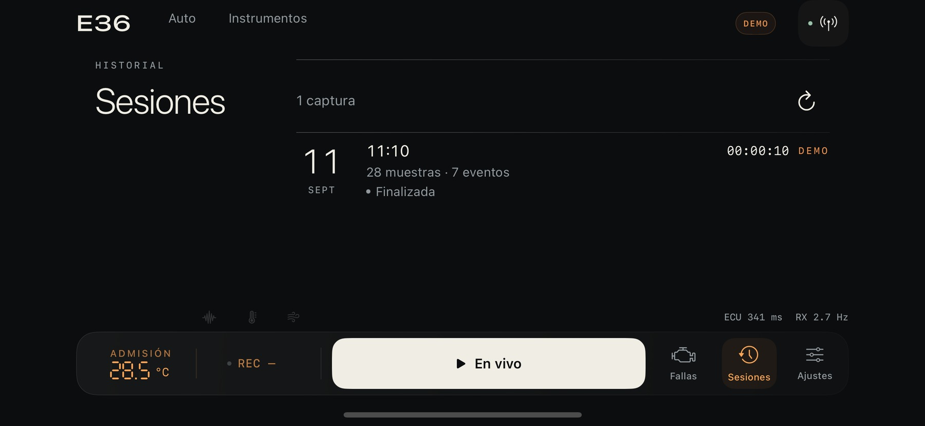
ios/Design/sessions-landscape.jpg
