IgnacioPardo/e36-obd/ios/Design/sessions-portrait.jpg

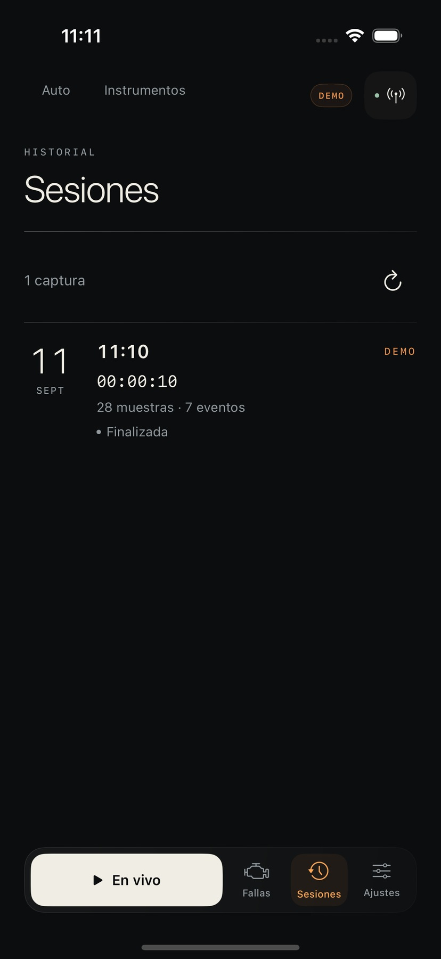
ios/Design/sessions-portrait.jpg
