IgnacioPardo/e36-obd/ios/Design/settings-landscape.jpg

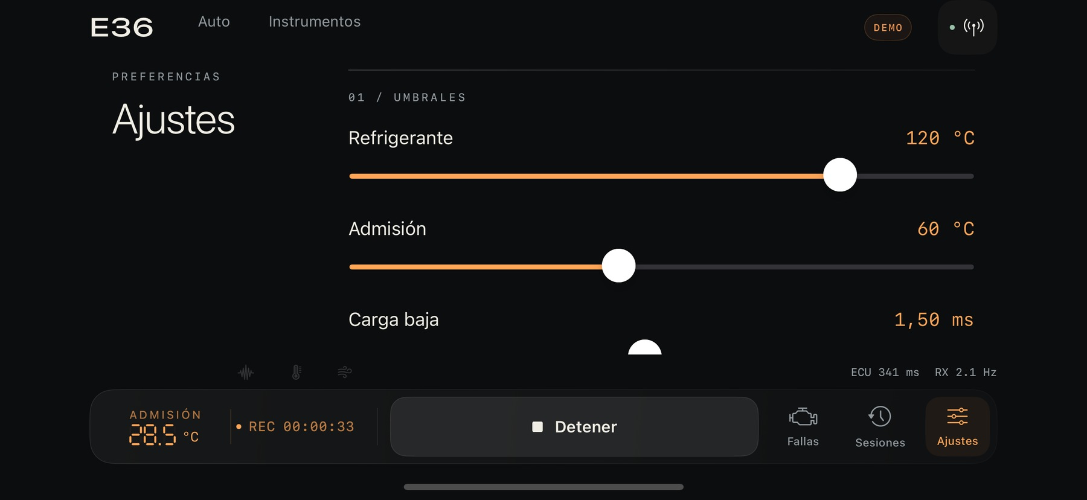
ios/Design/settings-landscape.jpg
