IgnacioPardo/e36-obd/ios/Design/settings-portrait.jpg

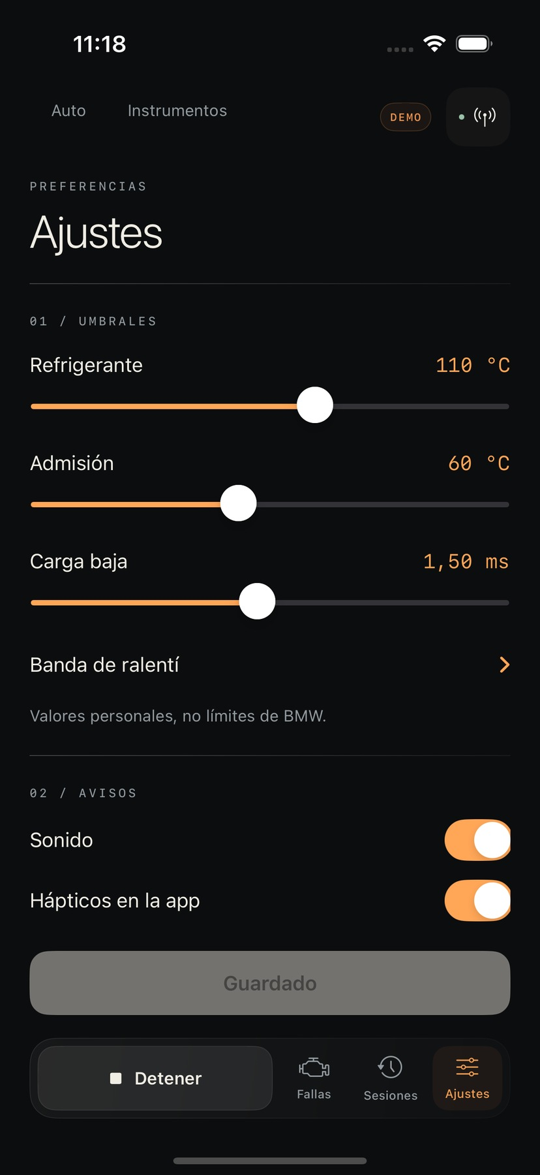
ios/Design/settings-portrait.jpg
