IgnacioPardo/e36-obd/ios/Design/vehicle-orbit.jpg

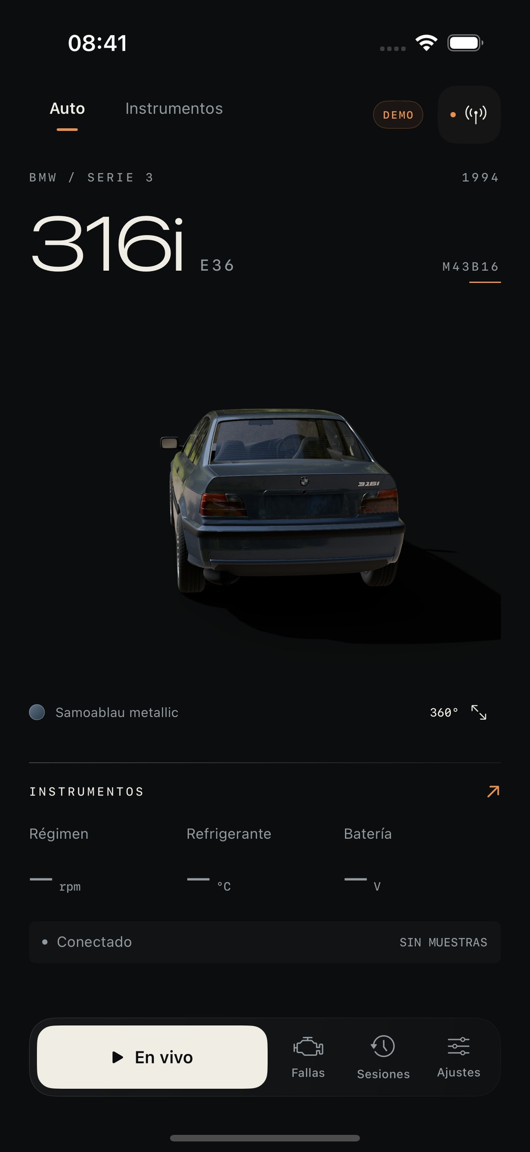
ios/Design/vehicle-orbit.jpg
