IgnacioPardo/e36-obd/ios/Design/Vehicle/AppLighting/rear.png

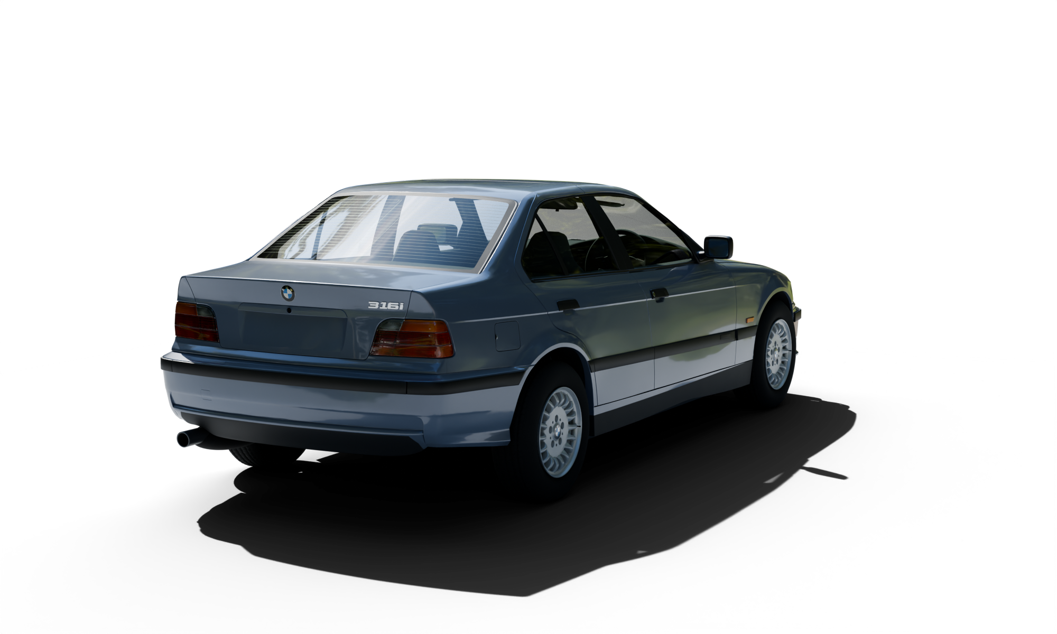
ios/Design/Vehicle/AppLighting/rear.png
