IgnacioPardo/e36-obd/ios/Design/Vehicle/front-fit-review.jpg

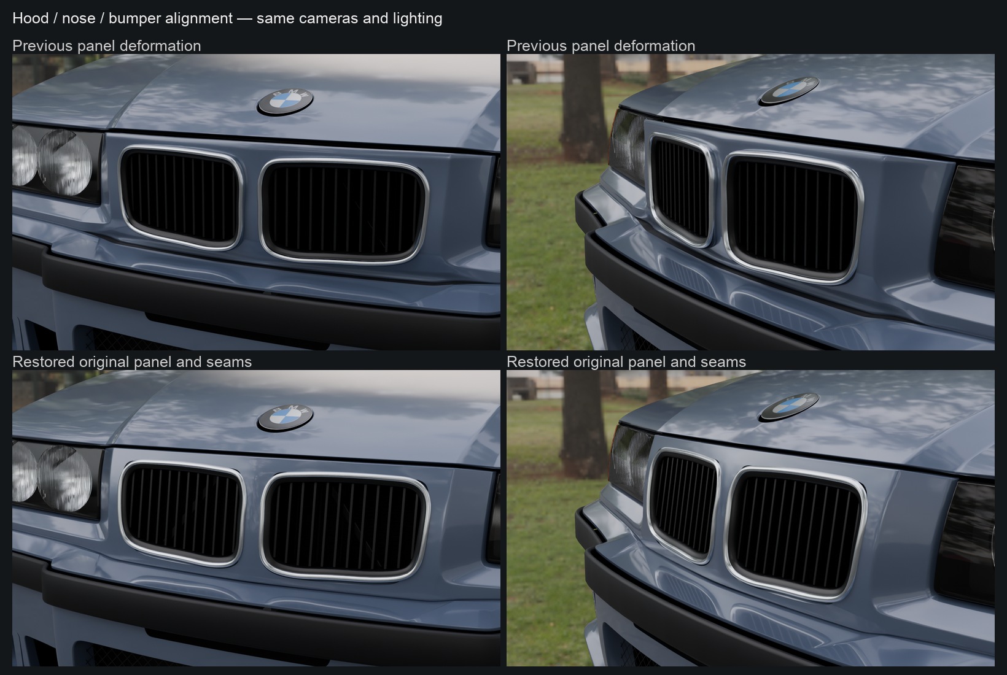
ios/Design/Vehicle/front-fit-review.jpg
