IgnacioPardo/e36-obd/ios/Design/Vehicle/FrontFit/duct.png

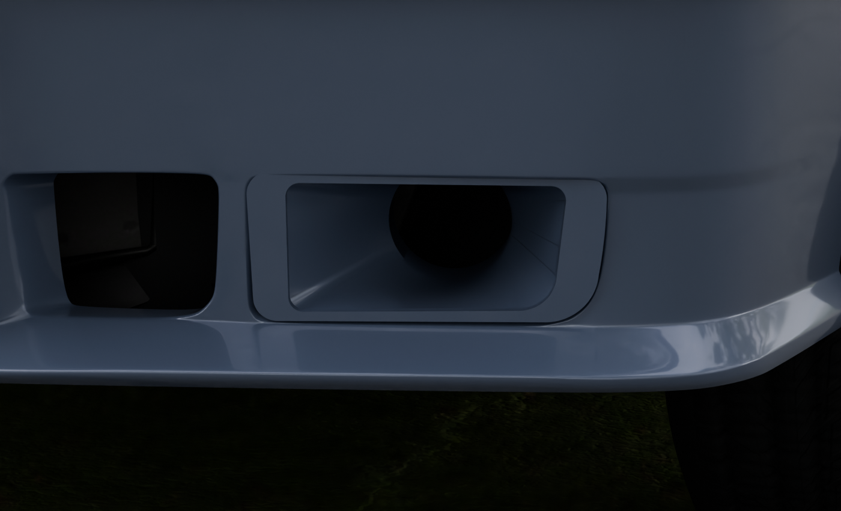
ios/Design/Vehicle/FrontFit/duct.png
