IgnacioPardo/e36-obd/ios/Design/Vehicle/FrontFit/grille-side.png

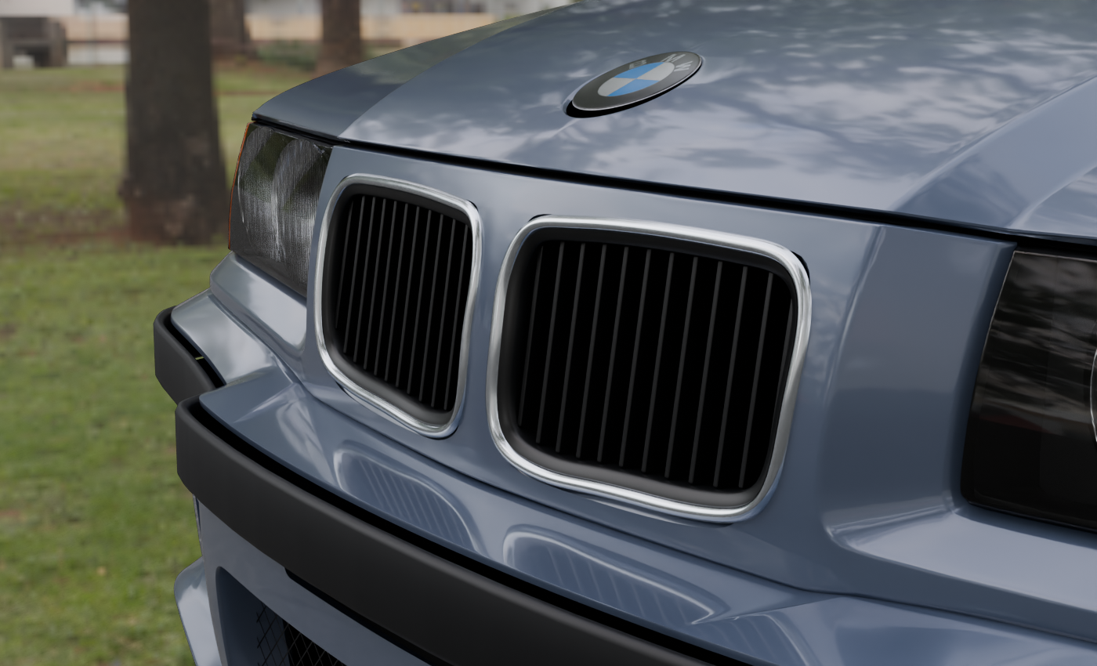
ios/Design/Vehicle/FrontFit/grille-side.png
