IgnacioPardo/e36-obd/ios/Design/Vehicle/FrontFit/grille.png

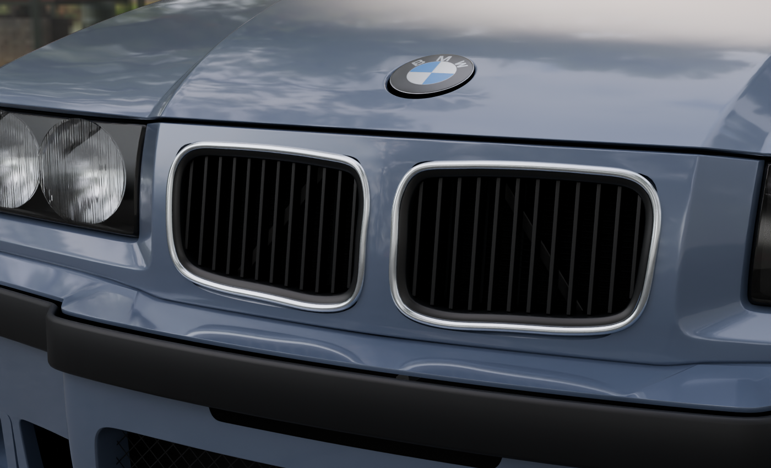
ios/Design/Vehicle/FrontFit/grille.png
