IgnacioPardo/e36-obd/ios/Design/Vehicle/FrontFit/lip.png

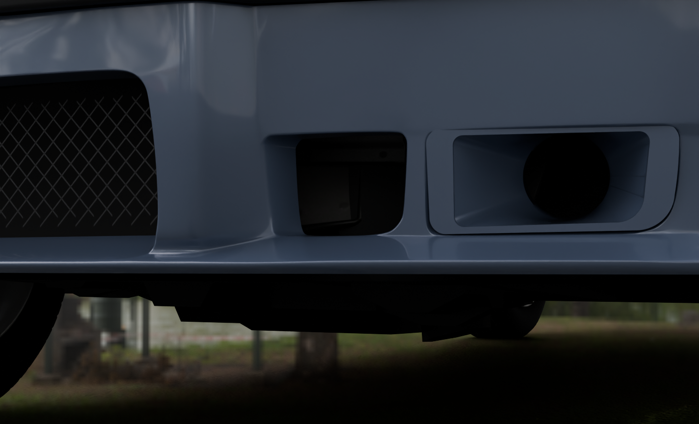
ios/Design/Vehicle/FrontFit/lip.png
