IgnacioPardo/e36-obd/ios/Design/Vehicle/HD/rear.png

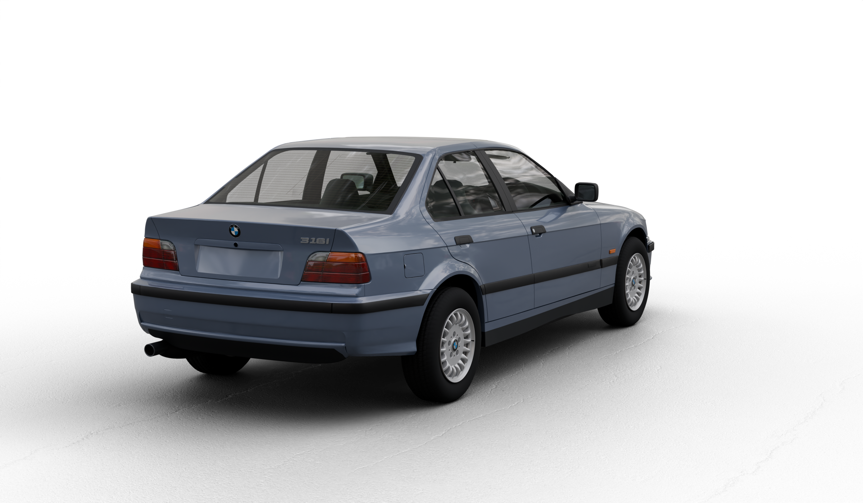
ios/Design/Vehicle/HD/rear.png
