IgnacioPardo/e36-obd/ios/Design/Vehicle/MetalReview/apron.png

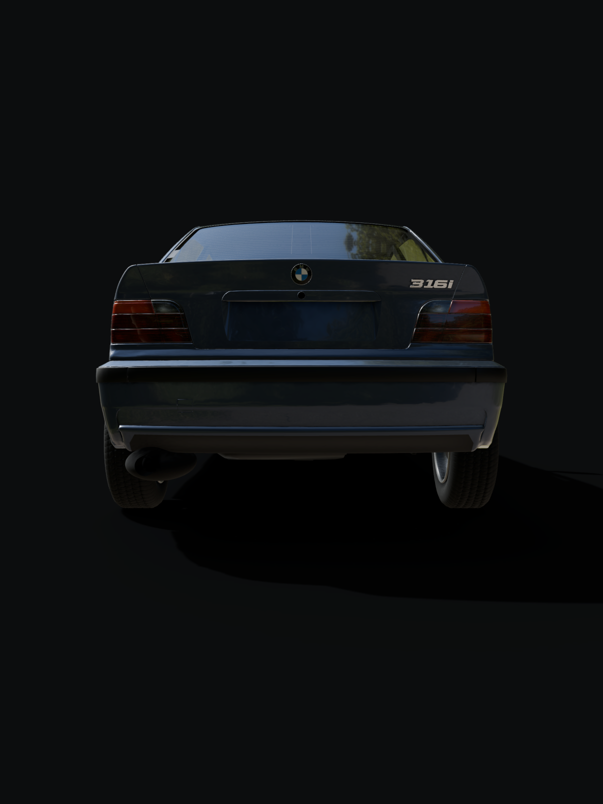
ios/Design/Vehicle/MetalReview/apron.png
