IgnacioPardo/e36-obd/ios/Design/Vehicle/MetalReview/cabin.png

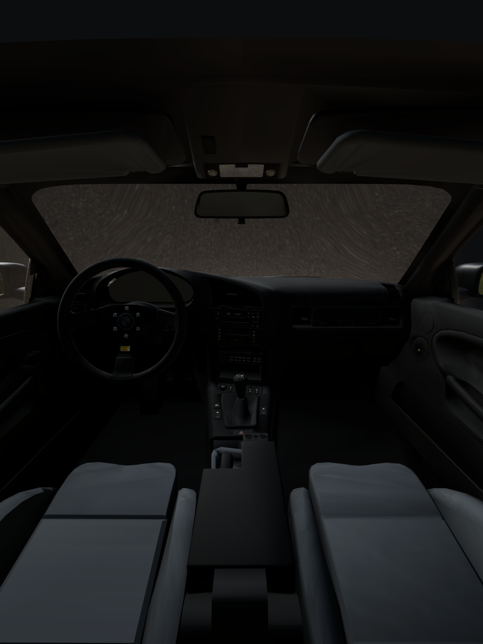
ios/Design/Vehicle/MetalReview/cabin.png
