IgnacioPardo/e36-obd/ios/Design/Vehicle/MetalReview/nose.png

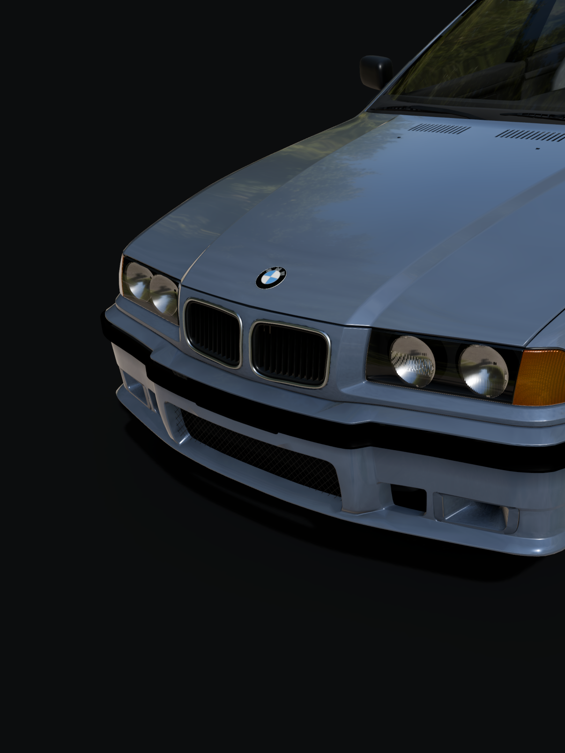
ios/Design/Vehicle/MetalReview/nose.png
