IgnacioPardo/e36-obd/ios/Design/Vehicle/MetalReview/optics.png

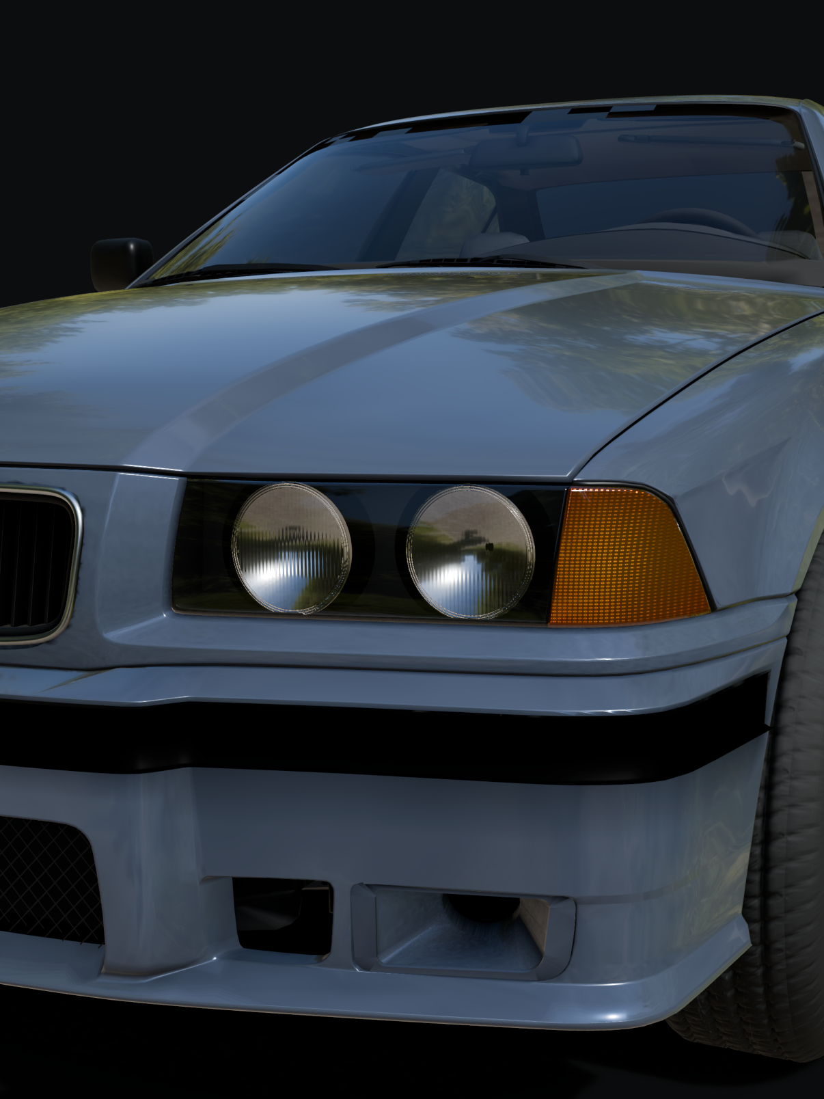
ios/Design/Vehicle/MetalReview/optics.png
