IgnacioPardo/e36-obd/ios/Design/Vehicle/MetalReview/rear.png

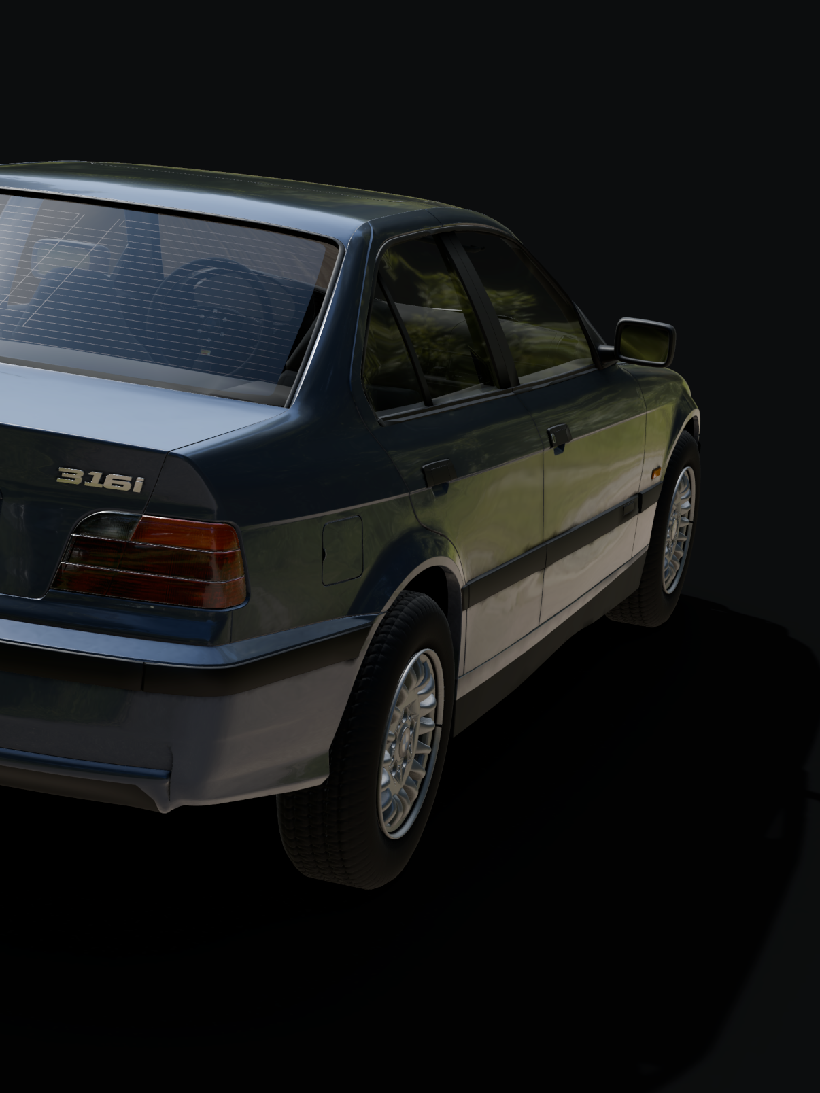
ios/Design/Vehicle/MetalReview/rear.png
