IgnacioPardo/e36-obd/ios/Design/Vehicle/MetalReview/side.png

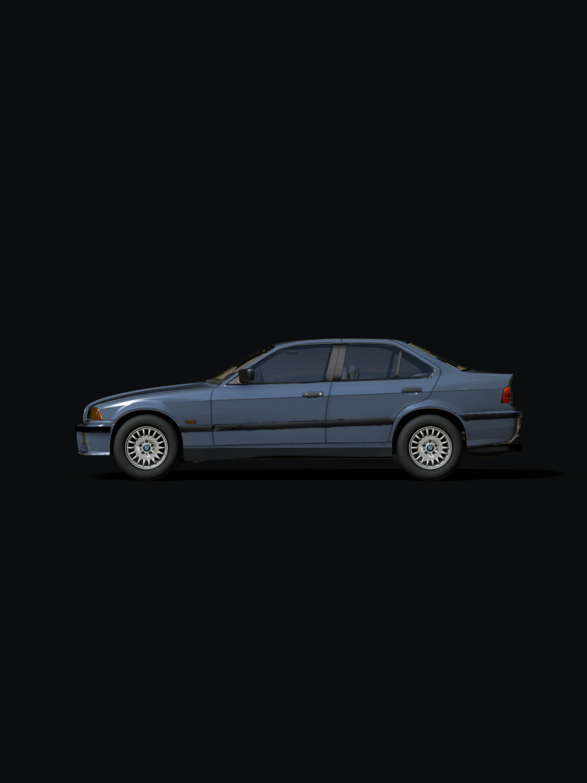
ios/Design/Vehicle/MetalReview/side.png
