IgnacioPardo/e36-obd/ios/Design/Vehicle/paint-samples.jpg

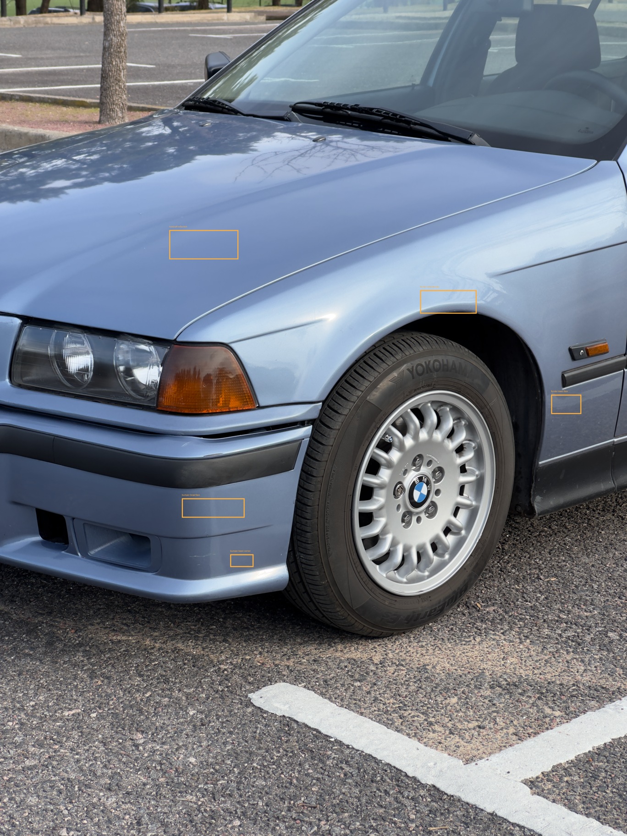
ios/Design/Vehicle/paint-samples.jpg
