IgnacioPardo/e36-obd/ios/Design/Vehicle/reference-comparison.jpg

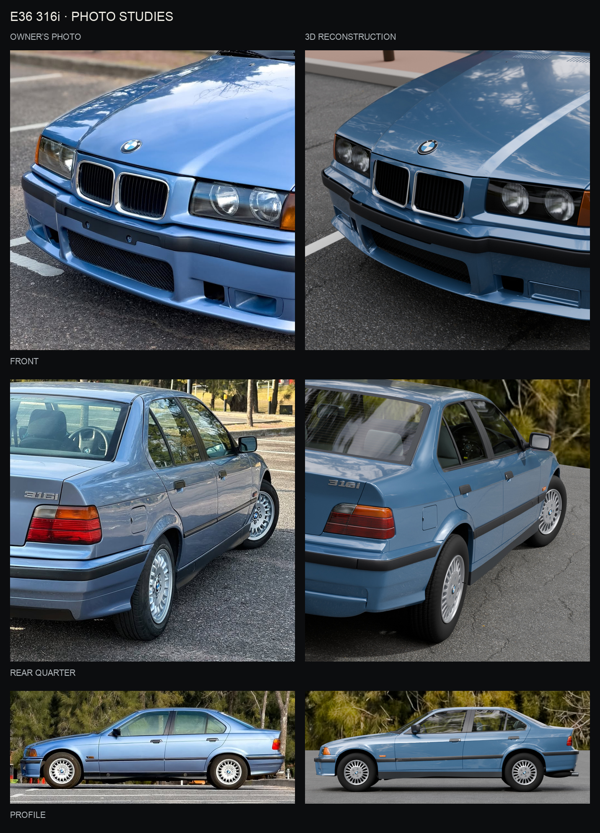
ios/Design/Vehicle/reference-comparison.jpg
