IgnacioPardo/e36-obd/ios/Design/Vehicle/reference-nose.jpg

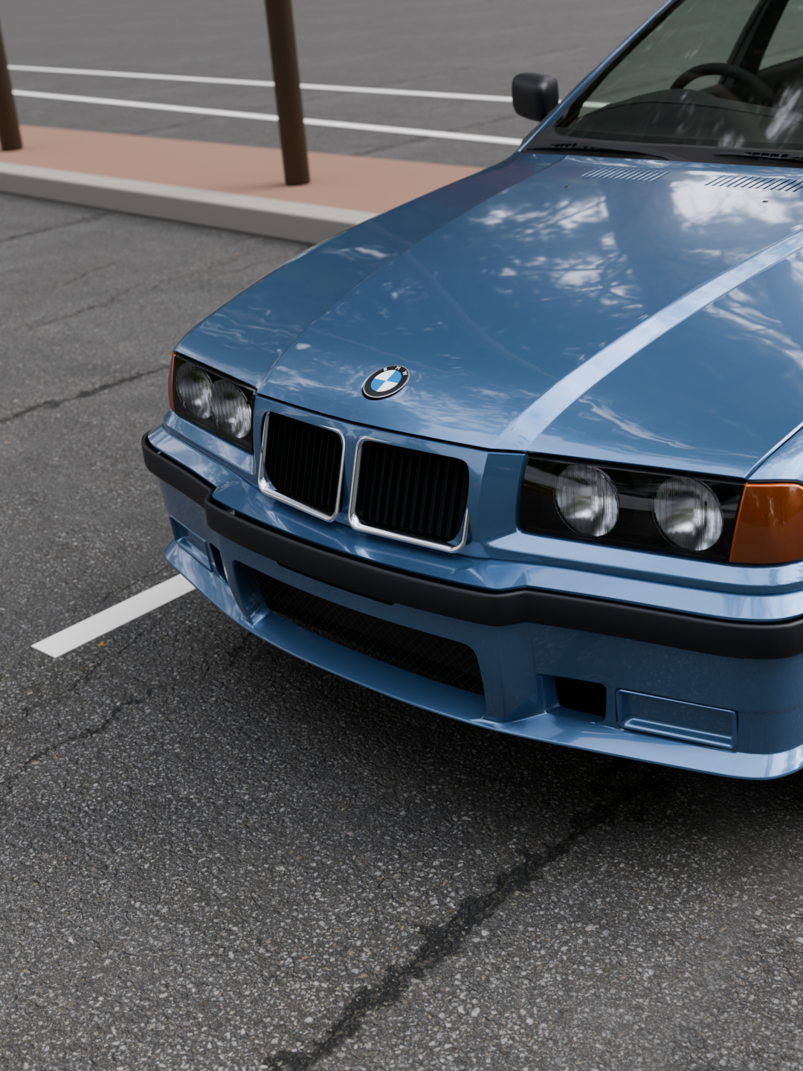
ios/Design/Vehicle/reference-nose.jpg
