IgnacioPardo/e36-obd/ios/Design/Vehicle/reference-rear.jpg

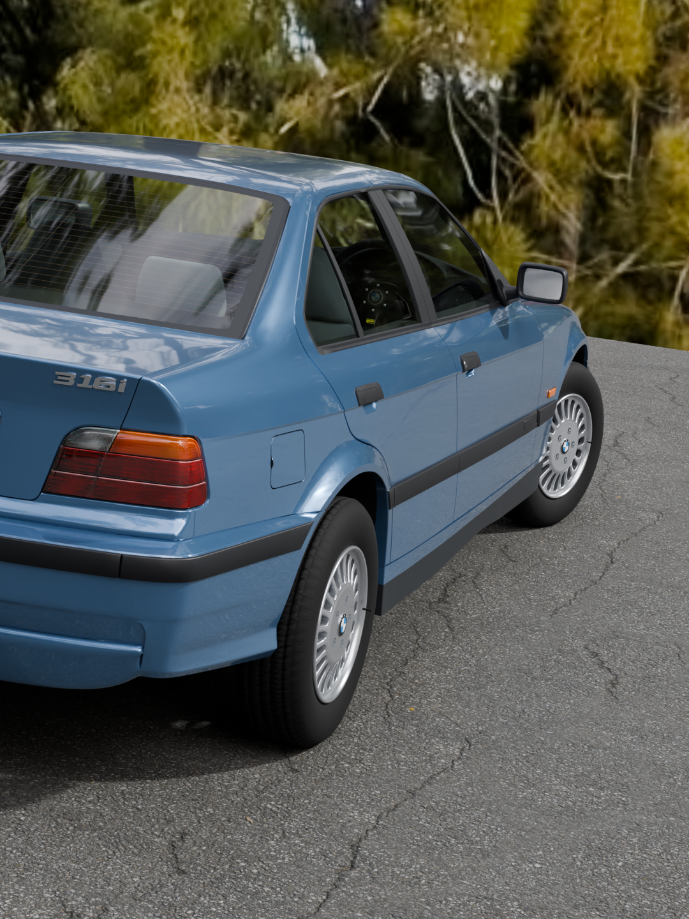
ios/Design/Vehicle/reference-rear.jpg
