IgnacioPardo/e36-obd/ios/Design/Vehicle/reference-side.jpg

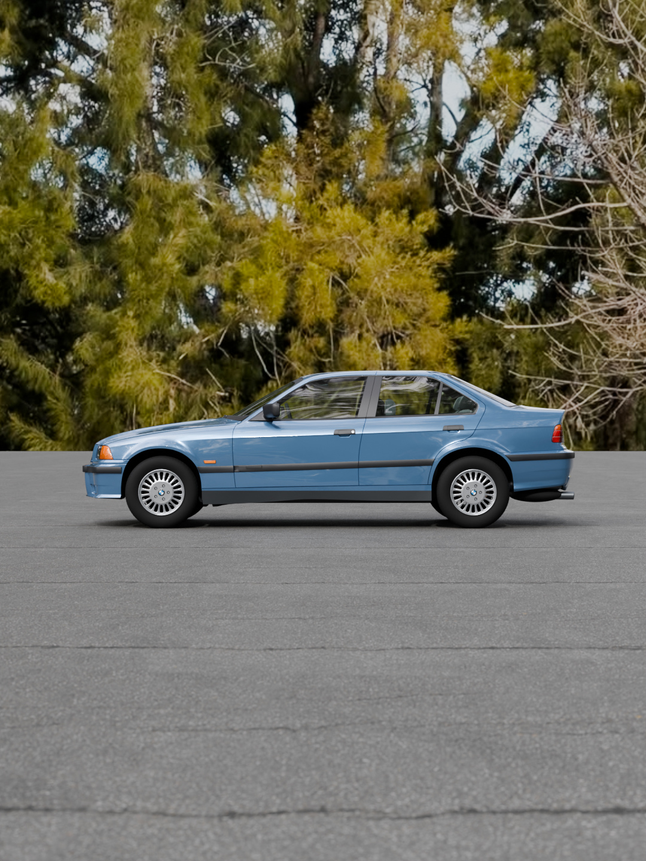
ios/Design/Vehicle/reference-side.jpg
