IgnacioPardo/e36-obd/ios/Design/Vehicle/Samoablau-review.jpg

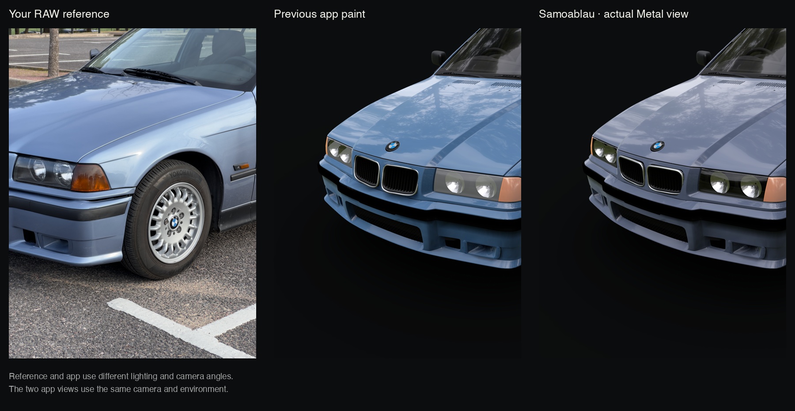
ios/Design/Vehicle/Samoablau-review.jpg
