IgnacioPardo/e36-obd/ios/Design/Vehicle/SceneStudy/app-landscape.png

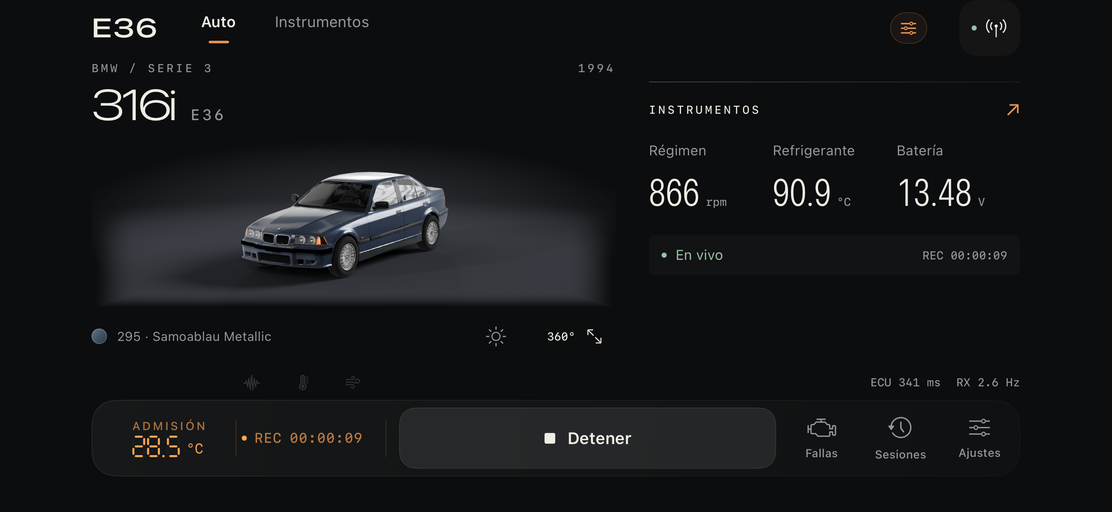
ios/Design/Vehicle/SceneStudy/app-landscape.png
