IgnacioPardo/e36-obd/ios/Design/Vehicle/SceneStudy/app-portrait.png

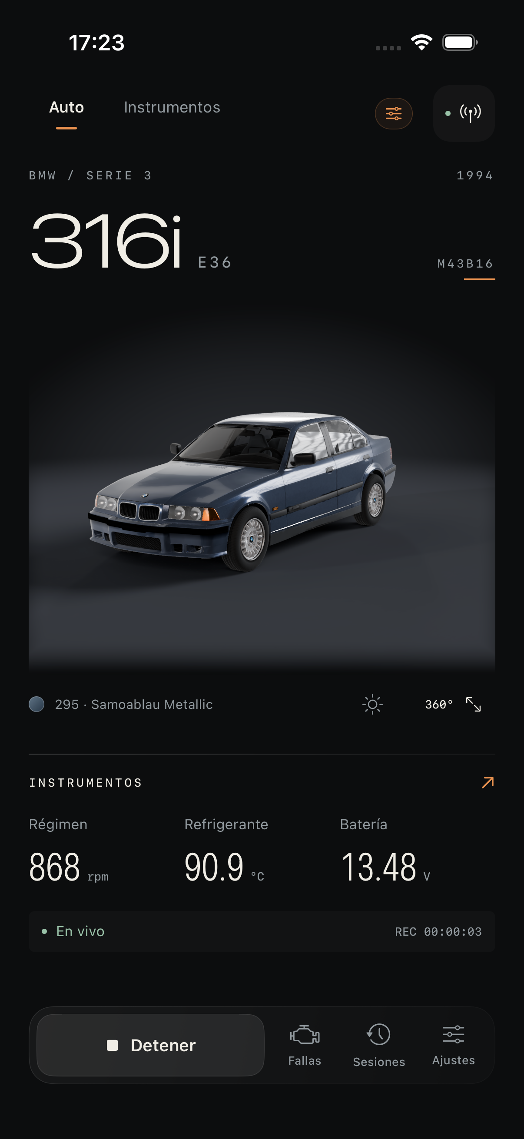
ios/Design/Vehicle/SceneStudy/app-portrait.png
