IgnacioPardo/e36-obd/ios/Design/Vehicle/SceneStudy/comparison.jpg

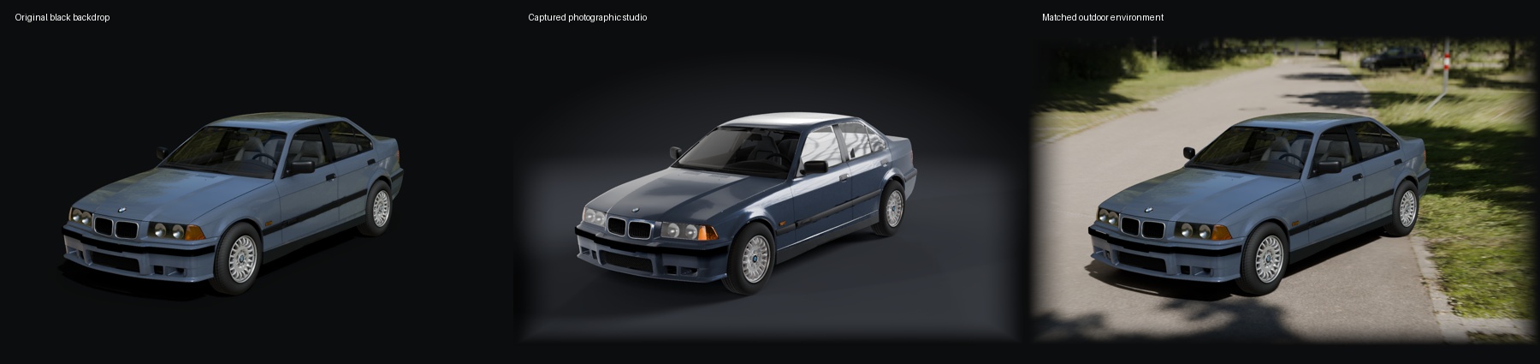
ios/Design/Vehicle/SceneStudy/comparison.jpg
