IgnacioPardo/e36-obd/ios/Design/Vehicle/SceneStudy/cycles-reference.png

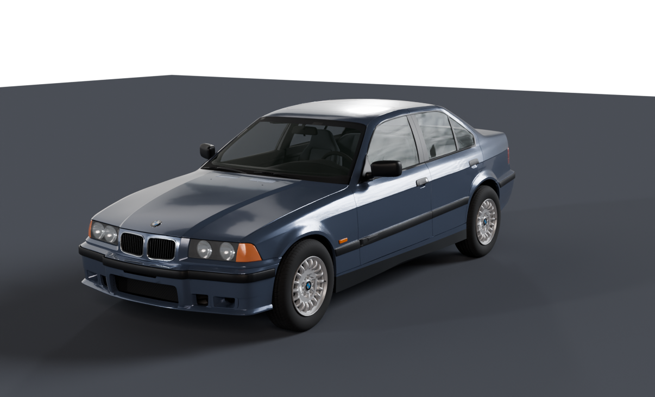
ios/Design/Vehicle/SceneStudy/cycles-reference.png
