IgnacioPardo/e36-obd/ios/Design/Vehicle/SceneStudy/exhaust.png

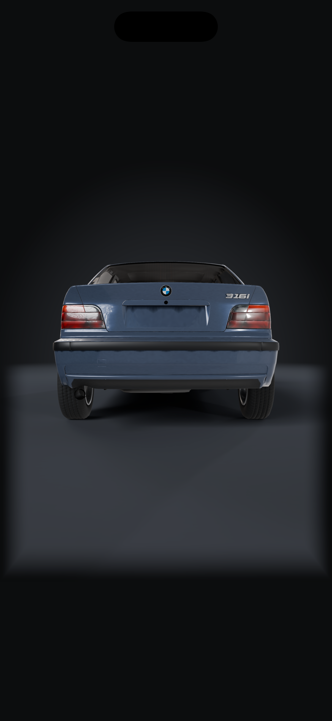
ios/Design/Vehicle/SceneStudy/exhaust.png
