IgnacioPardo/e36-obd/ios/Design/Vehicle/SceneStudy/exterior-landscape.png

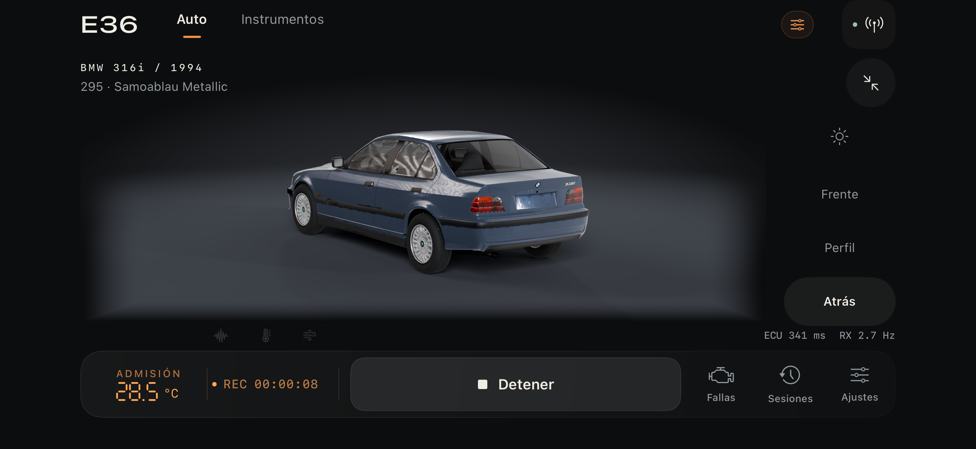
ios/Design/Vehicle/SceneStudy/exterior-landscape.png
