IgnacioPardo/e36-obd/ios/Design/Vehicle/SceneStudy/exterior-portrait.png

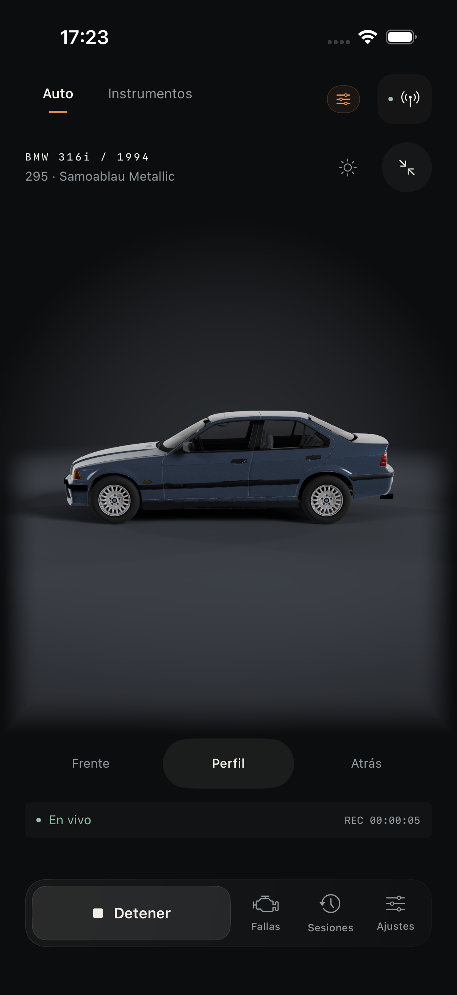
ios/Design/Vehicle/SceneStudy/exterior-portrait.png
