IgnacioPardo/e36-obd/ios/Design/Vehicle/SceneStudy/iteration-comparison.jpg

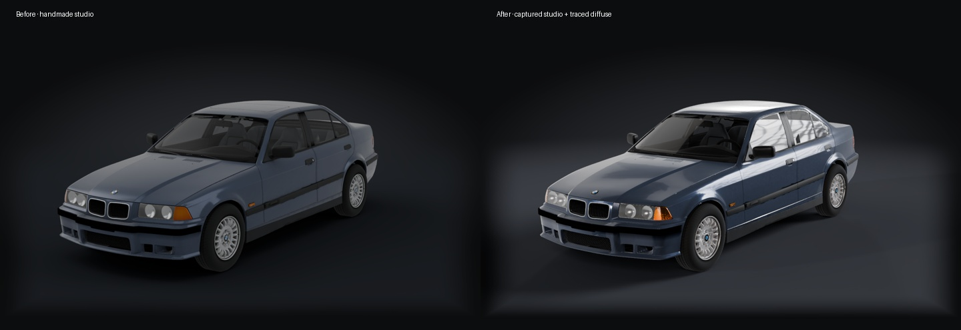
ios/Design/Vehicle/SceneStudy/iteration-comparison.jpg
