IgnacioPardo/e36-obd/ios/Design/Vehicle/SceneStudy/lighting-angles.jpg

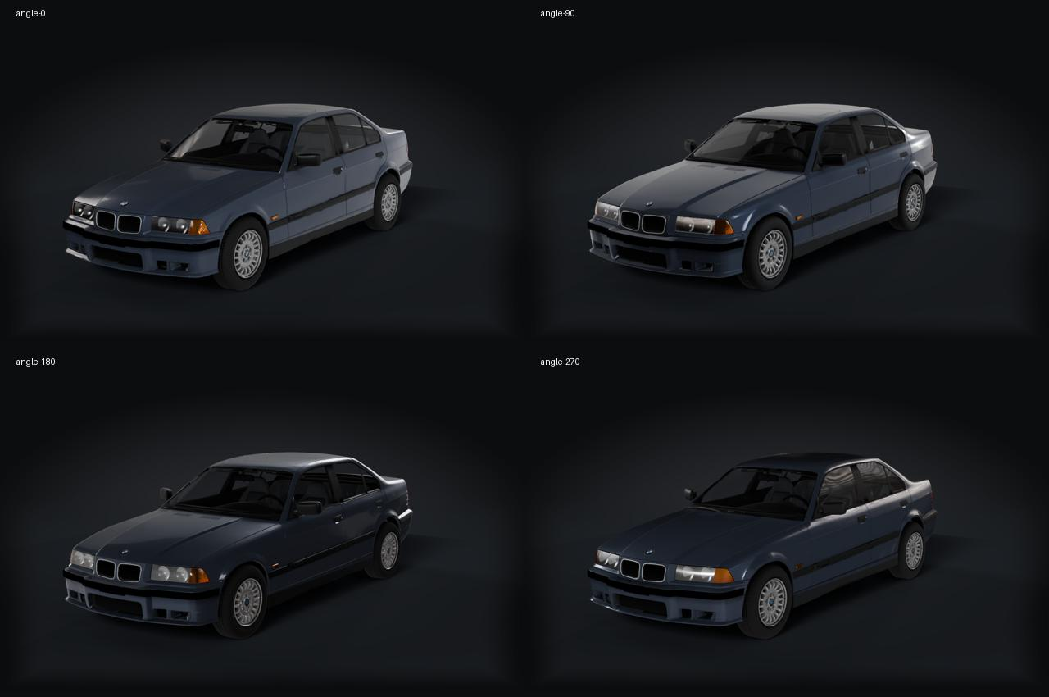
ios/Design/Vehicle/SceneStudy/lighting-angles.jpg
