IgnacioPardo/e36-obd/ios/Design/Vehicle/SceneStudy/lighting-exposure.jpg

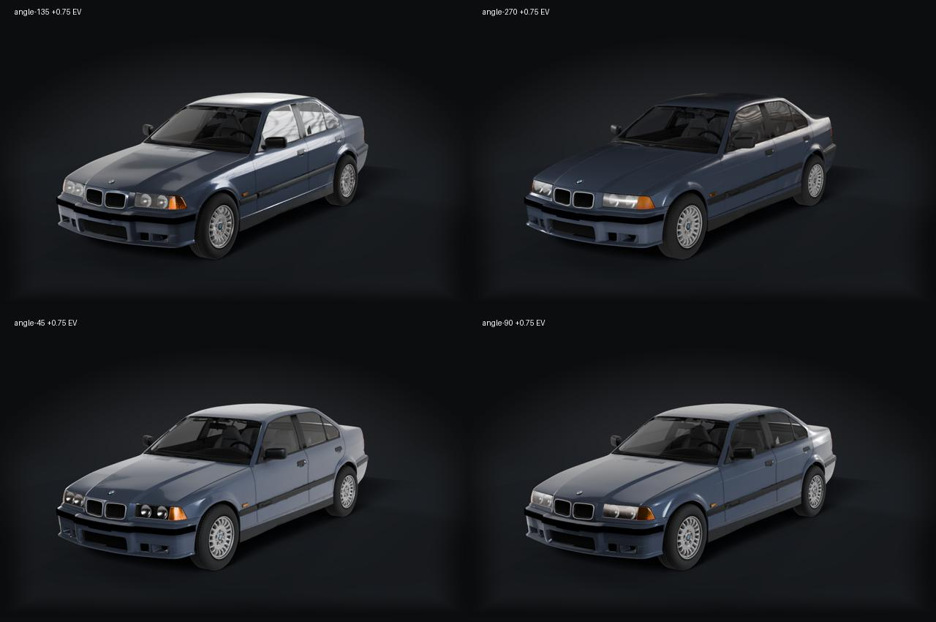
ios/Design/Vehicle/SceneStudy/lighting-exposure.jpg
