IgnacioPardo/e36-obd/ios/Design/Vehicle/SceneStudy/original.png

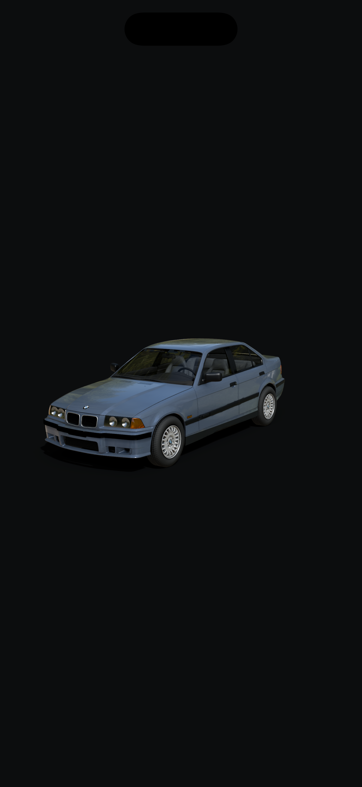
ios/Design/Vehicle/SceneStudy/original.png
