IgnacioPardo/e36-obd/ios/Design/Vehicle/SceneStudy/outdoor.png

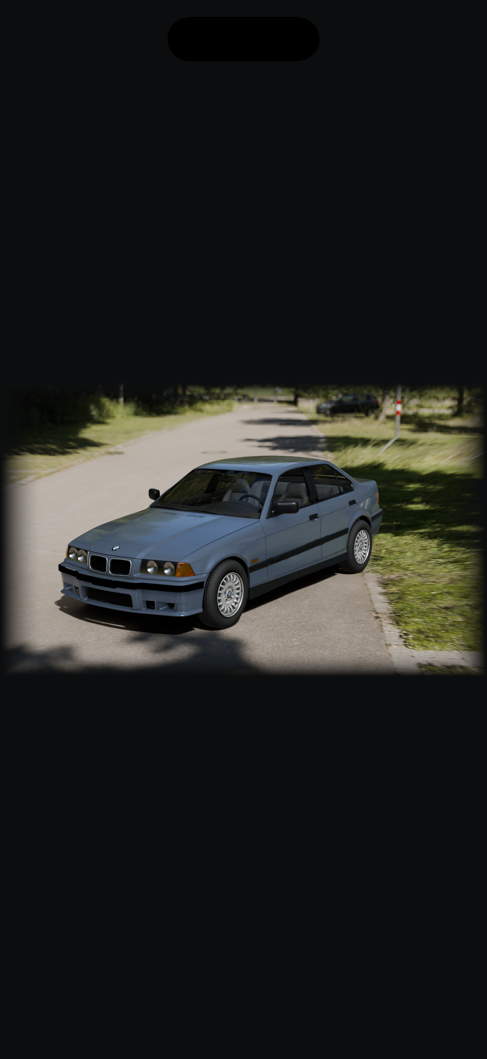
ios/Design/Vehicle/SceneStudy/outdoor.png
