IgnacioPardo/e36-obd/ios/Design/Vehicle/SceneStudy/studio.png

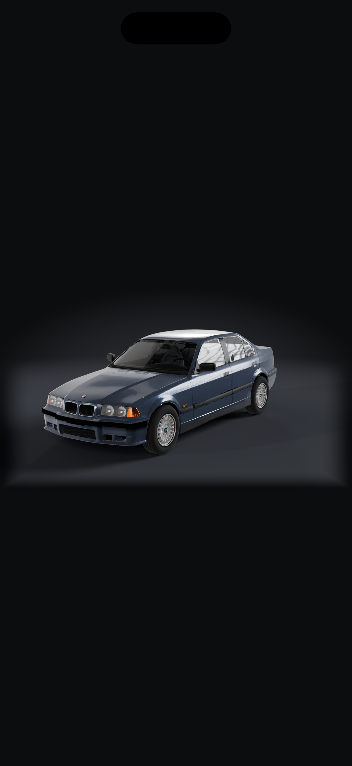
ios/Design/Vehicle/SceneStudy/studio.png
