IgnacioPardo/e36-obd/ios/Design/Vehicle/SceneStudy/widget-source.png

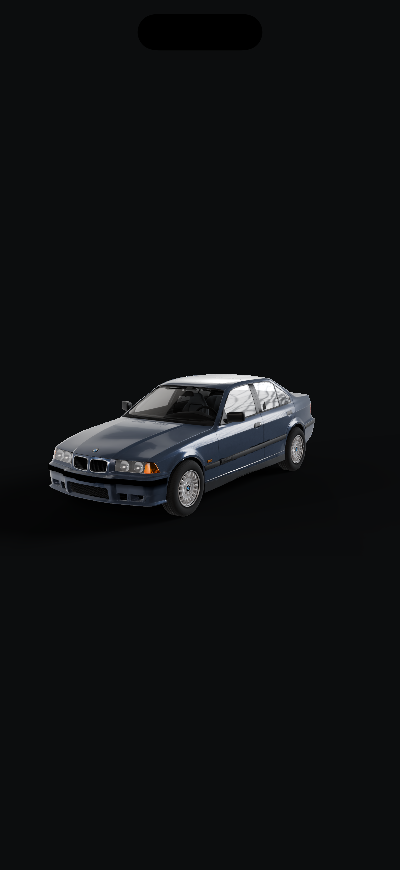
ios/Design/Vehicle/SceneStudy/widget-source.png
