IgnacioPardo/e36-obd/ios/Design/Vehicle/wheel-study.png

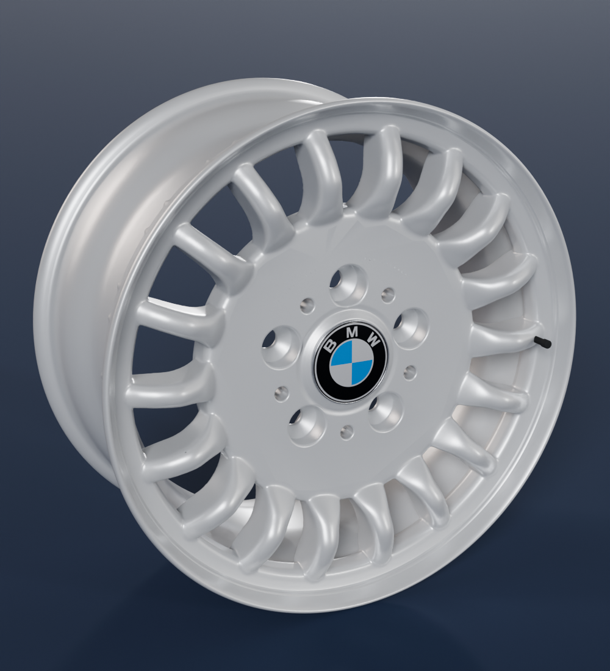
ios/Design/Vehicle/wheel-study.png
