IgnacioPardo/e36-obd/ios/Design/Widgets/empty.png

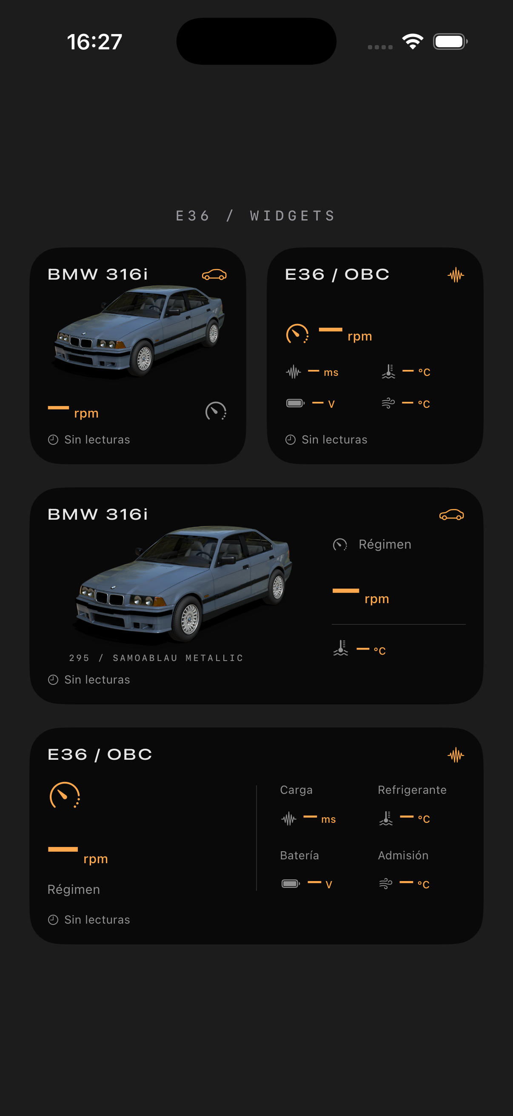
ios/Design/Widgets/empty.png
