IgnacioPardo/e36-obd/ios/Design/Widgets/exterior-landscape.png

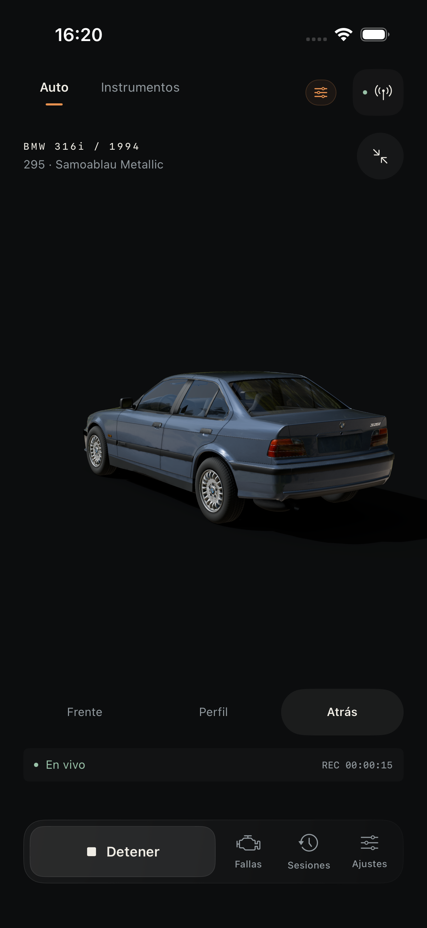
ios/Design/Widgets/exterior-landscape.png
