IgnacioPardo/e36-obd/ios/Design/Widgets/headlamp-cover.png

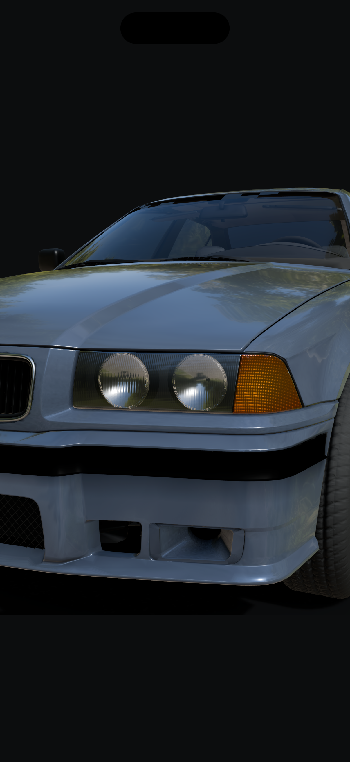
ios/Design/Widgets/headlamp-cover.png
