IgnacioPardo/e36-obd/ios/Design/Widgets/headlamp-detail.png

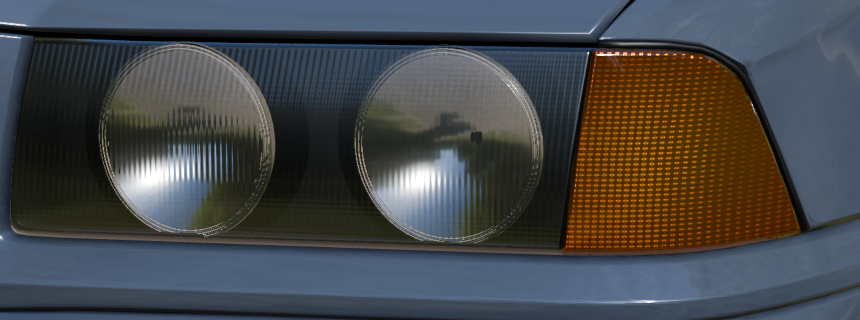
ios/Design/Widgets/headlamp-detail.png
