IgnacioPardo/e36-obd/ios/Design/Widgets/large-garage-compact.png

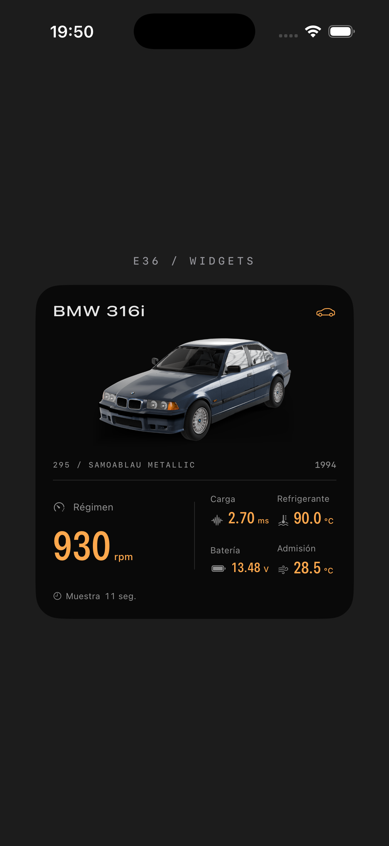
ios/Design/Widgets/large-garage-compact.png
