IgnacioPardo/e36-obd/ios/Design/Widgets/large-obc-compact.png

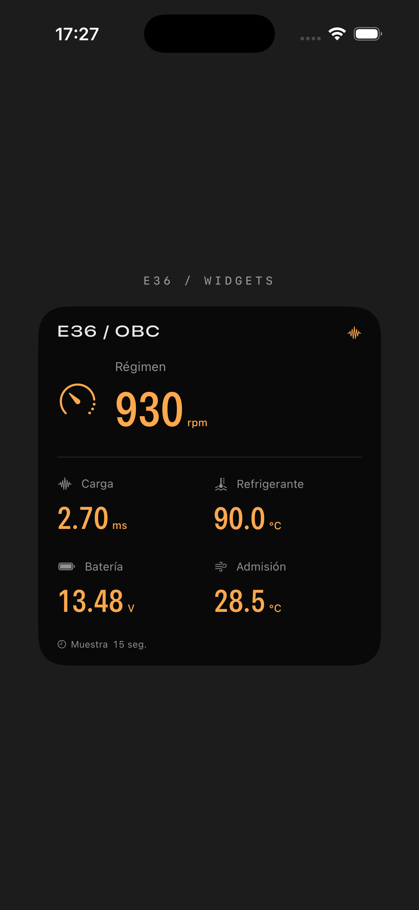
ios/Design/Widgets/large-obc-compact.png
