IgnacioPardo/e36-obd/ios/Design/Widgets/large-obc.png

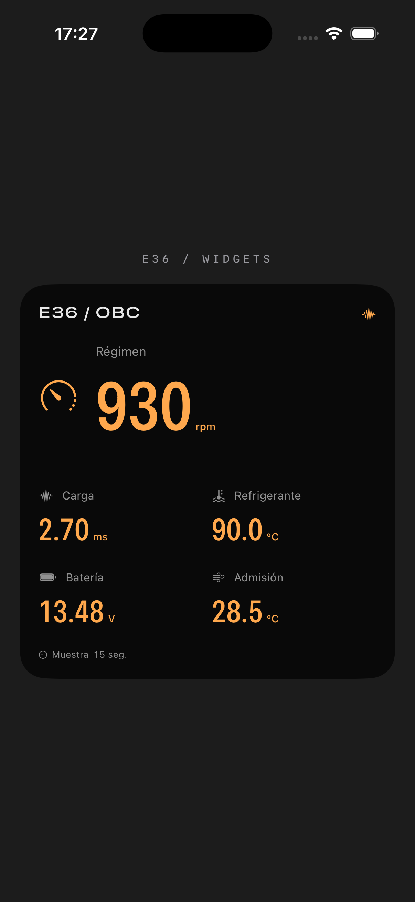
ios/Design/Widgets/large-obc.png
