IgnacioPardo/e36-obd/ios/Design/Widgets/live-activity.png

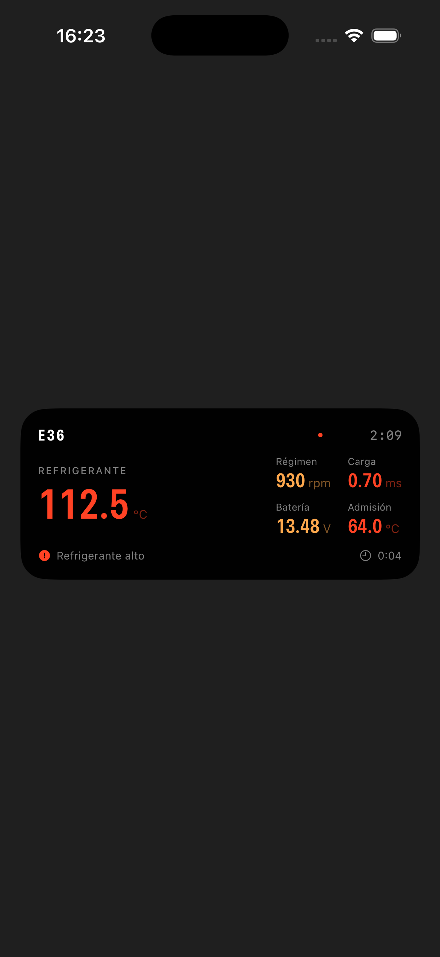
ios/Design/Widgets/live-activity.png
