IgnacioPardo/e36-obd/ios/Design/Widgets/review-sheet.jpg

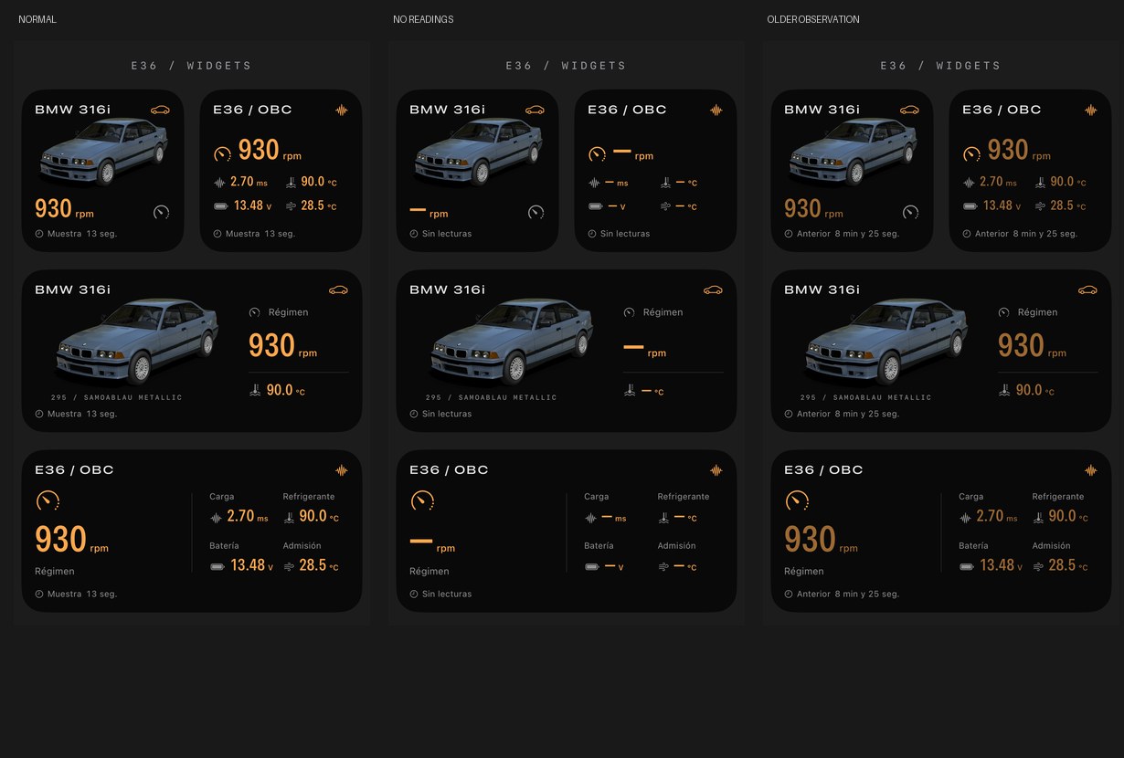
ios/Design/Widgets/review-sheet.jpg
