IgnacioPardo/e36-obd/ios/Design/Widgets/watch-rpm.png

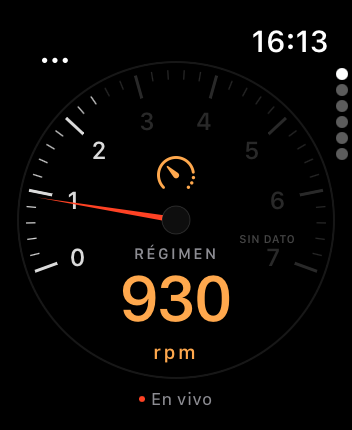
ios/Design/Widgets/watch-rpm.png
