IgnacioPardo/e36-obd/ios/E36OBD/VehicleScene/ContactShadow.png

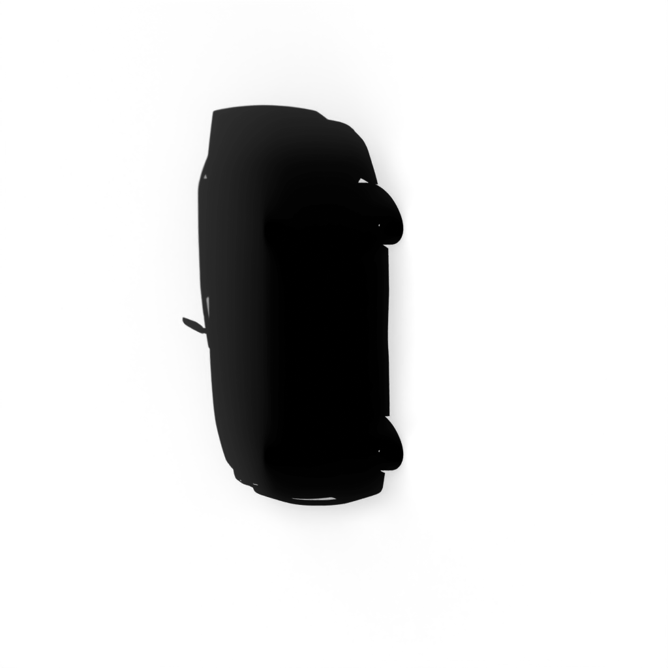
ios/E36OBD/VehicleScene/ContactShadow.png
