IgnacioPardo/e36-obd/ios/E36OBD/VehicleScene/SoftboxShadow.png

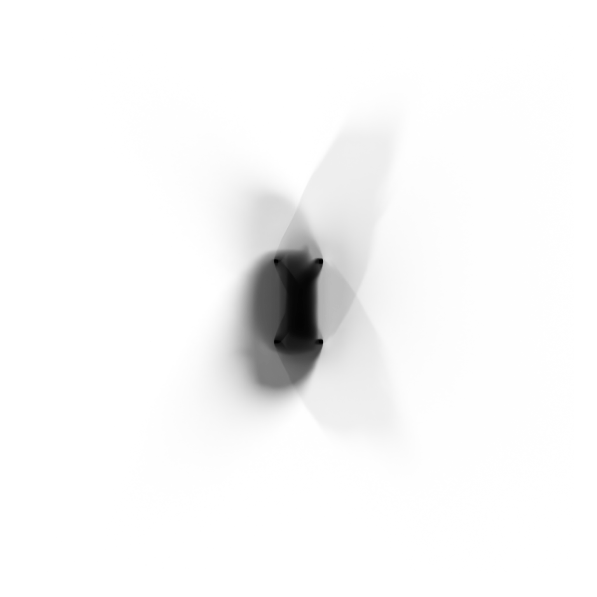
ios/E36OBD/VehicleScene/SoftboxShadow.png
