IgnacioPardo/e36-obd/hardware/elm-backpack/exports/exploded-views/assembly-raw.png

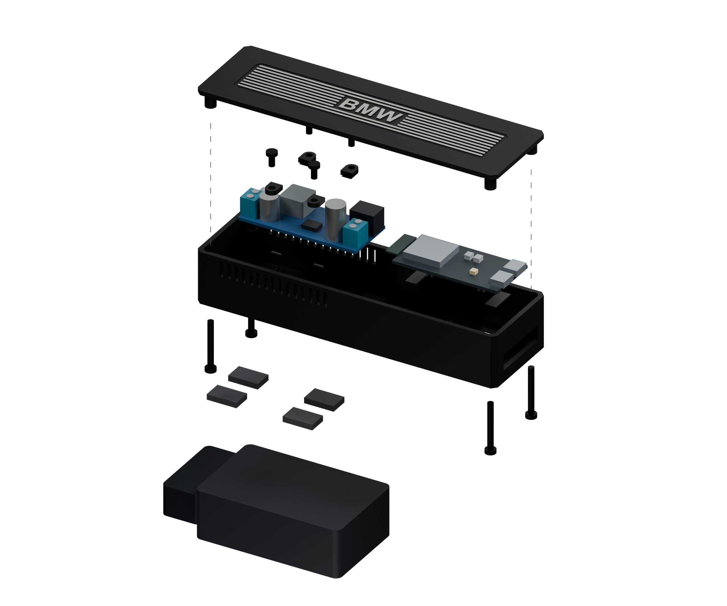
hardware/elm-backpack/exports/exploded-views/assembly-raw.png
