IgnacioPardo/e36-obd/hardware/elm-backpack/exports/exploded-views/assembly.png

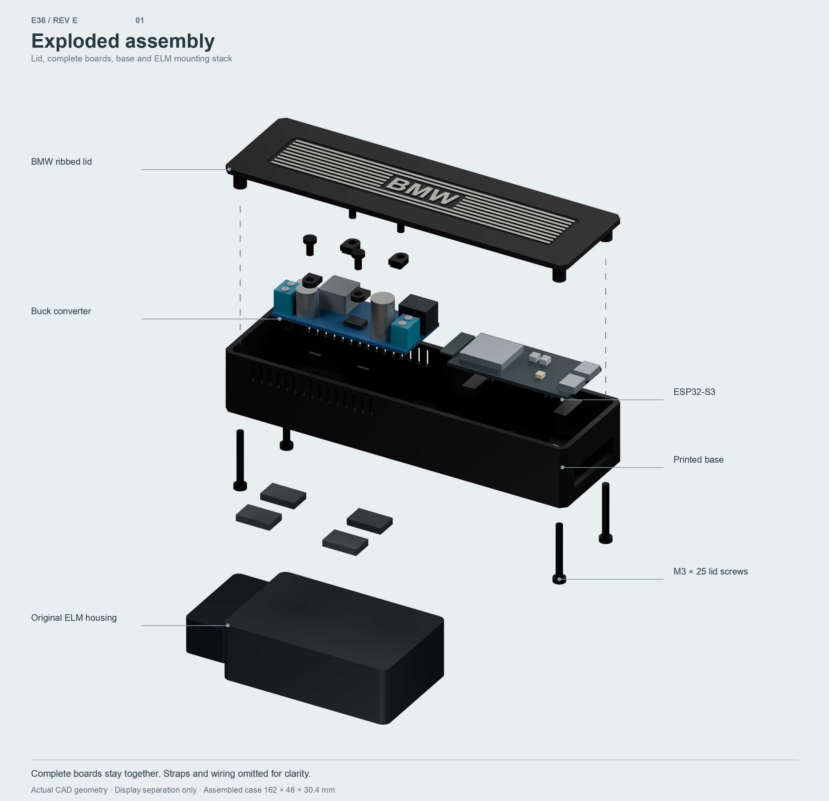
hardware/elm-backpack/exports/exploded-views/assembly.png
